acQuire-KL/VT_PCB_PCA/_From_Cornel/Scavenger - V4.4 Cornel 24-09-19/UC_Version4/MFG_PACK -- 3904-30028-06 -- UC_v4.4/BOM_3904-30028-06 - PCA, Scavenger - MCU, ver 4.4.xlsx

Seq | Level | VTPN | Description | ECO | Qty | UoM | RefDes | Populate | BOM Notes | Type | LifeCycle | MFG | MPN | Per Assy. | Unit € | Value € | Vendor | Parts Master Notes | MOQ | Pack Qty | LT
1 | Parent | 3904-30028-06 | PCA, Scavenger - Control (MCU), Ver 4.4 |  | 1 | ea |  |  |  | Make | Production | ECAS | 3904-30028-06 | 1 | 0.0000 | 2.78 |  | 0.0000 | 0 | 0 | 0
2 | 1 | 4200-00020-00 | CAP, 3v7 39mAh Hybrid Layer Capacitor, 15x20, 3-pin Solder Tags |  | 1 | ea | BT1 |  |  | Buy | Production | LongSing Technology | HPC-1520 | 1 | 2.7757 | 2.7757 | LongSing Technology Group | 0.0000 | 500 | 500 | 4
3 | 1 | 4000-00000-00 | Test point / Mounting Hole / Fudicials / Non Component on PCB |  | 1 | ea | BT2 | DNP |  | Reference Item | Production | none | none | 1 | 0.0000 |  |  | 0.0000 | 0 | 0 | 0
4 | 1 | 4106-00020-00 | CAP 0603 (1608_m), 100n, 5%, 25V X7R |  | 8 | ea | C1,C8,C13,C14,C27,C28,C29,C49 |  |  | Buy | Production | Yageo | CC0603JRX7R8BB104 | 8 | 0.0043 | 0.0347 | ECAS | 0.0000 | 4000 | 0 | 16
5 | 1 | 4106-00010-00 | CAP 0603 (1608_m), 10p, 10%, 25V X7R |  | 4 | ea | C2,C3,C50,C51 |  |  | Buy | Production | Kyocera AVX | 06033C100KAT2A | 4 | 0.0019 | 0.0076 | ECAS | 0.0000 | 4000 | 0 | 12
6 | 1 | 4112-00100-00 | CAP 1206 (3216_m), 10u, 10%, 25V X7R |  | 4 | ea | C4,C7,C11,C30 |  |  | Buy | Production | Samsung | CL31B106KAHNFNE | 4 | 0.0254 | 0.1015 | ECAS | 0.0000 | 2000 | 0 | 22
7 | 1 | 4106-00100-00 | CAP 0603 (1608_m), 1u, 10%, 25V X7R |  | 4 | ea | C5,C6,C9,C10 |  |  | Buy | Production | Samsung | CL10B105KA8VPNC | 4 | 0.0140 | 0.0560 | ECAS | 0.0000 | 4000 | 0 | 22
8 | 1 | 4112-00120-00 | CAP 1206 (3216_m), 4u7, 10%, 25V X7R |  | 1 | ea | C12 |  |  | Buy | Production | Taiyo Yuden | MSAST31LAB7475KTNA01 | 1 | 0.0442 | 0.0442 | ECAS | 0.0000 | 2000 | 0 | 19
9 | 1 | 4510-00020-00 | DIO, GP Diode 75V 150mA, SOD-123F |  | 1 | ea | D1 |  |  | Buy | Production | Diotec | 1N4148W | 1 | 0.0121 | 0.0121 | ECAS | 0.0000 | 3000 | 0 | 20
10 | 1 | 4510-00030-00 | DIO, Clamp Ipp TVS, SOD-923 |  | 1 | ea | D2 |  |  | Buy | Production | OnSemi | ESD9B5.0ST5G | 1 | 0.0237 | 0.0237 | 0.0000 | 0.0000 | 8000 | 8000 | 12
11 | 1 | 4000-00000-00 | Test point / Mounting Hole / Fudicials / Non Component on PCB |  | 4 | ea | FID1,FID2,FID3,FID4 | DNP |  | Reference Item | Production | none | none | 4 | 0.0000 |  |  | 0.0000 | 0 | 0 | 0
12 | 1 | 4722-00010-00 | FIL, RLC EMI Filter 3rd Order Low Pass 6 Channel R = 40Ohms, C = 12pF, L = 20nH 16-UFDFN Exposed Pad |  | 1 | ea | FL1 |  |  | Buy | Obsolete | On Semi | CM1624-08DE | 1 | 0.2950 | 0.2950 | ECAS | 0.0000 | 3000 | 0 | 12
13 | 1 | 4000-00000-00 | Test point / Mounting Hole / Fudicials / Non Component on PCB |  | 3 | ea | H1,H2,H3 | DNP |  | Reference Item | Production | none | none | 3 | 0.0000 |  |  | 0.0000 | 0 | 0 | 0
14 | 1 | 4000-00000-00 | Test point / Mounting Hole / Fudicials / Non Component on PCB |  | 1 | ea | J1 | DNP |  | Reference Item | Production | none | none | 1 | 0.0000 |  |  | 0.0000 | 0 | 0 | 0
15 | 1 | 4412-00020-00 | CON, 2x3-pin Turned Contacts, F, THP W2B, P=2.54mm, 3A |  | 1 | ea | J3 |  |  | Buy | Production | Connfly | DS1002-03-2*3131 | 1 | 0.2100 | 0.2100 | ECAS | 0.0000 | 800 | 0 | 30
16 | 1 | 4401-00020-00 | CON, 1x4-pin, Straight, THP, B2B Male Header, P=2.54mm, 3A |  | 1 | ea | J4 |  |  | Buy | Production | Connfly | DS1021-1*4SF11-B | 1 | 0.0198 | 0.0198 | TME | 0.0000 | 2000 | 2000 | 22
17 | 1 | 4750-00010-00 | REL, DPDT-NO (2 Form C) SMD, 3V 46.66mA, 2A |  | 1 | ea | K1 |  |  | Buy | Production | Fujitsu | FTR-B4GA003Z | 1 | 0.8000 | 0.8000 | ECAS | 0.0000 | 1000 | 0 | 14
18 | 1 | 4500-00020-00 | TRN, BJT NPN - Pre-Biased 50 V 100mA 200mW, SMD, SOT-346 |  | 1 | ea | Q2 |  |  | Buy | Production | Rohm | DTC143TKAT146 | 1 | 0.0182 | 0.0182 | ECAS | Confirm Package | 3000 | 0 | 13
19 | 1 | 4006-00170-00 | RES 0603 (1608_m), 10K, 1%, 1/10W, Thick Film |  | 3 | ea | R1,R2,R4 |  |  | Buy | Production | Walsin | WR06X1002FTL | 3 | 0.0012 | 0.0036 | ECAS | 0.0000 | 5000 | 0 | 26
20 | 1 | 4006-00001-00 | RES 0603 (1608_m), 0R (Jumper), 1%, 1/10W, Thick Film |  | 1 | ea | R3 |  |  | Buy | Production | Vishay Dale | CRCW06030000Z0EA | 1 | 0.0010 | 0.0010 | ECAS | 0.0000 | 5000 | 0 | 37
21 | 1 | 4006-00100-00 | RES 0603 (1608_m), 1K, 1%, 1/10W, Thick Film |  | 1 | ea | R64 |  |  | Buy | Production | Walsin | WR06X1001FTL | 1 | 0.0012 | 0.0012 | ECAS | 0.0000 | 5000 | 0 | 26
22 | 1 | 4414-00010-00 | CON, 8-Pos microSD Cage, Hinged, SMD |  | 1 | ea | SD-Card1 |  |  | Buy | Production | Wurth | 693072010801 | 1 | 0.9500 | 0.9500 | Wurth | 0.0000 | 1000 | 1 | 15
23 | 1 | 4751-00010-00 | SWI, Molded Body Reed SPST-NO 10 ~ 30AT Operate Range 10W 500mA (AC/DC) 140V SMD |  | 1 | ea | SW1 |  |  | Buy | Production | Coto Technology | CT10-1030-G1 | 1 | 0.5832 | 0.5832 | Digikey | [04/11/23] Direct ECAS to Digikey pricing | 2000 | 0 | 32
24 | 1 | 4000-00000-00 | Test point / Mounting Hole / Fudicials / Non Component on PCB |  | 1 | ea | TP1 |  |  | Reference Item | Production | none | none | 1 | 0.0000 |  |  | 0.0000 | 0 | 0 | 0
25 | 1 | 4704-00010-00 | MCU, ARM® Cortex®-M33 STM32U5 32-Bit 160MHz 2MB (2M x 8) FLASH 64-LQFP (10x10) |  | 1 | ea | U1 |  |  | Free Issue | Production | ST Micro | STM32U575RIT6 | 1 | 5.7100 | 5.7100 |  | VT purchased 10kpcs @ €5.71 | 1 | 0 | 10
26 | 1 | 4522-00020-00 | REG, 3v3 300mA LDO Linear Voltage Regulator, SOT-25 |  | 2 | ea | U2,U6 |  |  | Buy | Production | Diodes Inc | AP7343DQ-33W5-7 | 2 | 0.0949 | 0.1898 | ECAS | 0.0000 | 3000 | 0 | 8
27 | 1 | 4410-00010-00 | CON, 2x18-Pos, F, PCI, SMD, P=1.00mm, Black |  | 1 | ea | U3 |  |  | Buy | Production | Amphenol | 10061913-100CLF | 1 | 2.2400 | 2.2400 | ECAS | [13/09/23] RFQ to Avnet | 2450 | 1 | 10
28 | 1 | 4718-00010-00 | MEM, EEPROM Memory IC 512Kbit (64x8) I²C 1MHz 900ns 8-SOIC |  | 1 | ea | U4 |  |  | Buy | Production | On Semi | CAT24C512XE-T2 | 1 | 0.7202 | 0.7202 | Digikey | [14/11/23] EBV offer "XI" (-40~+85C not "XE" -40~+125C) 6k EAU, 1k8 reel @ €0.90; 8-weeks. [02/02/24] Alternative packages 8-TSSOP (CAT24C512YI-GT3) @ €0.4865 @ 3k reel | 381 | 0 | 1
29 | 1 | 4720-00010-00 | ICS, Supervisor 3v0VDF N-ch Open Drain 1-Ch SSOT-24 |  | 1 | ea | U9 |  |  | Buy | Production | Torex | XC6120N302NR-G | 1 | 0.1800 | 0.1800 | ECAS | 0.0000 | 1000 | 1000 | 18
30 | 1 | 4714-00020-00 | CRY, 16MHz ±10ppm Crystal 10pF 80Ohms 4-SMD, No Lead |  | 1 | ea | XTAL1 |  |  | Buy | Production | CTS Frequency Controls | 403C11A16M00000 | 1 | 0.3187 | 0.3187 | ECAS | [07/12/23] Jauch offer O 16,0-JXS32-10-10/10-LF 1k @ $0.35 | 3000 | 0 | 12
31 | 1 | 4714-00010-00 | CRY, 32.768kHz ±10ppm 6pF 70kOhms 2-SMD, No Lead |  | 1 | ea | Y1 |  |  | Buy | Production | ECS Inc | ECS-.327-6-34B-C-TR | 1 | 0.3777 | 0.3777 | Digikey | [07/12/23] Jauch offer Q 0,032768-JTX310-6-10-T1-LF 1k @ $0.25 | 3000 | 0 | 15
32 | 1 | 4904-30028-05 | PCB, Scavenger MCU (32x107x1.6mm, 4L, 1ox/1oz, ENIG, 4-up), ver4.4 |  | 1 | ea | PCB1 |  |  | Buy | Production | EMS Approved | 4904-30028-05 | 1 | 1.0000 | 1.0000 | 0.0000 | 0.0000 | 0 | 0 | 0
