acQuire-KL/VT_PCB_PCA/_From_Cornel/Scavenger - V4.4 Cornel 24-10-31/BG95_Version4_4L/MFG_PACK 3902-30029-07/3902-30029-07_BOM -- Comms BG95 v4.4.xlsx

Sheet: BOM
Seq | Level | VTPN | Description | ECO | Qty | UoM | RefDes | Populate | BOM Notes | Type | LifeCycle | MFG | MPN | Per Assy. | Unit € | Value € | Vendor | Parts Master Notes | MOQ | Pack Qty | LT
1 | Parent | 3902-30029-07 | PCA, Scavenger - Communications (GSM), BG95, Ver 4.4 - EUR |  | 1 | ea |  |  |  | Make | Production | ECAS | 0.00 | 1 | 0.0000 | 16.03 |  | 0.0000 | 0 | 0 | 0
2 | 1 | 4200-00020-00 | CAP, 3v7 39mAh Hybrid Layer Capacitor, 15x20, 3-pin Solder Tags |  | 1 | ea | BT1 |  |  | Buy | Production | LongSing Technology | HPC-1520 | 1 | 2.6969 | 2.6969 | LongSing Technology Group | 0.0000 | 500 | 500 | 0
3 | 1 | 4106-00040-00 | CAP 0603 (1608_m), 33p, 5%, 50V NP0 |  | 3 | ea | C1,C2,C3 |  |  | Buy | Production | Darfon | C1608NP0330JGTS | 3 | 0.0019 | 0.0058 | ECAS | 0.0000 | 4000 | 4000 | 0
4 | 1 | 4106-00020-00 | CAP 0603 (1608_m), 100n, 10%, 16V X7R |  | 3 | ea | C4,C7,C8 |  |  | Buy | Production | Darfon | C1005X7R104KETS | 3 | 0.0005 | 0.0015 | Schukat | 0.0000 | 4000 | 4000 | 0
5 | 1 | 4128-00100-00 | CAP 2917 (7343_m), 470u, 10%, 6v3 Tant |  | 2 | ea | C5,C6 |  |  | Buy | Production | Kyocera AVX | TAJD477K006RNJ | 2 | 0.5600 | 1.1200 | ECAS | 0.0000 | 500 | 500 | 0
6 | 1 | 4106-00040-00 | CAP 0603 (1608_m), 33p, 5%, 50V NP0 |  | 2 | ea | C9,C10 | DNP |  | Buy | Production | Darfon | C1608NP0330JGTS | 2 | 0.0019 | 0.0039 | ECAS | 0.0000 | 4000 | 4000 | 0
7 | 1 | 4106-00010-00 | CAP 0603 (1608_m), 10p, 5%, 50V NP0 |  | 2 | ea | C11,C12 |  |  | Buy | Production | Darfon | C1608NP0100JGTS | 2 | 0.0019 | 0.0038 | ECAS | 0.0000 | 4000 | 4000 | 0
8 | 1 | 4006-00000-00 | RES 0603 Place Holder |  | 2 | ea | C13,C14 | DNP |  | Reference Item | Production | none | none | 2 | 0.0000 |  |  | 0.0000 | 0 | 0 | 0
9 | 1 | 4724-00010-00 | TVS, 5-Ch, 12.5V Clamp 8A (8/20µs) Ipp, SC-70-6 |  | 1 | ea | D1 |  |  | Buy | Production | Semtech | SMF05C.TCT | 1 | 0.2448 | 0.2448 | ECAS | 0.0000 | 3000 | 0 | 0
10 | 1 | 4000-00000-00 | Test point / Mounting Hole / Fudicials / Non Component on PCB |  | 4 | ea | FID1,FID2,FID3,FID4 |  |  | Reference Item | Production | none | none | 4 | 0.0000 |  |  | 0.0000 | 0 | 0 | 0
11 | 1 | 4000-00000-00 | Test point / Mounting Hole / Fudicials / Non Component on PCB |  | 1 | ea | H1 |  |  | Reference Item | Production | none | none | 1 | 0.0000 |  |  | 0.0000 | 0 | 0 | 0
12 | 1 | 4402-00020-00 | CON, 2x5-pin, Straight, SMD, B2B Male Header, P=2.54mm, 3A |  | 1 | ea | J2 |  |  | Buy | Production | Amphenol FCI | 95278-102B10LF | 1 | 0.3668 | 0.3668 | ECAS | 0.0000 | 5000 | 0 | 0
13 | 1 | 4402-00030-00 | CON, 2x8-pin, Straight, SMD, B2B Male Header, P=2.54mm, 3A |  | 1 | ea | J3 |  |  | Buy | Production | Amphenol FCI | 95278-102B16LF | 1 | 0.4309 | 0.4309 | ECAS | 0.0000 | 1 | 0 | 0
14 | 1 | 4753-00010-00 | HDW, Cable Clamp, SMD, 5x5x2mm, Ø1.0 ~ 1.5mm |  | 3 | ea | J4,J5,J6 |  |  | Buy | Production | Harwin | S8111-46R | 3 | 0.1331 | 0.3994 | Digikey | 0.0000 | 1500 | 1500 | 0
15 | 1 | 4414-00020-00 | CON, 6-Pos MicroSIM Cage, Push-Pull, No Detect, SMD |  | 1 | ea | J11 |  | • Fit "Test SIM" before starting initial Test • Replace with "Final SIM" after passing Test | Buy | Production | Molex | 78646-3001 | 1 | 0.7900 | 0.7900 | ECAS | RFQ before next build | 57 | 1 | 0
16 | 1 | 4416-00010-00 | CON, U.FL (UMCC) Jack, Male Pin 50Ohm SMD |  | 1 | ea | J12 |  |  | Buy | Production | TE Connectivity | 2337019-1 | 1 | 0.0061 | 0.0061 | ECAS | 0.0000 | 55 | 1 | 0
17 | 1 | 4500-00020-00 | TRN, BJT NPN - Pre-Biased R1=4K7 R2=0R, Vce=50V 100mA 200mW, SMD, TO-236-3, SC-59, SOT-23-3 |  | 3 | ea | Q1,Q3,Q8 |  |  | Buy | Production | Rohm | DTC143TKAT146 | 3 | 0.0182 | 0.0547 | ECAS | Confirm Package | 3000 | 0 | 0
18 | 1 | 4530-00010-00 | FET, P-Channel 30 V 6.5A (Ta) 3.1W (Ta), 8-SOP |  | 1 | ea | Q2 |  |  | Buy | Production | UMW | AO4459 | 1 | 0.0630 | 0.0630 | ECAS | 0.0000 | 500 | 1 | 0
19 | 1 | 4006-00160-00 | RES 0603 (1608_m), 15K, 1%, 1/10W, Thick Film |  | 1 | ea | R1 |  |  | Buy | Production | Vishay | CRCW060315K0FKEA | 1 | 0.0010 | 0.0010 | Schukat | 0.0000 | 5000 | 5000 | 0
20 | 1 | 4006-00150-00 | RES 0603 (1608_m), 4K7, 1%, 1/10W, Thick Film |  | 2 | ea | R2,R3 |  |  | Buy | Production | Vishay | CRCW06034K70FKEA | 2 | 0.0012 | 0.0023 | Schukat | 0.0000 | 5000 | 5000 | 0
21 | 1 | 4006-00001-00 | RES 0603 (1608_m), 0R (Jumper), 1%, 1/10W, Thick Film |  | 1 | ea | R4 |  |  | Buy | Production | Vishay Dale | CRCW06030000Z0EA | 1 | 0.0009 | 0.0009 | Schukat | 0.0000 | 5000 | 5000 | 0
22 | 1 | 4000-00000-00 | Test point / Mounting Hole / Fudicials / Non Component on PCB |  | 1 | ea | TP1 |  |  | Reference Item | Production | none | none | 1 | 0.0000 |  |  | 0.0000 | 0 | 0 | 0
23 | 1 | 4716-00010-00 | MDM, Cellular, GSM, LTE Transceiver Module 850MHz, 900MHz, 1.8GHz, 1.9GHz, SMD Module, No Antenna |  | 1 | ea | U1 |  |  | Buy | Production | Quectel | BG95M3LA-64-SGNS | 1 | 8.6749 | 8.6749 | FMG Electronics | [21/11/23] FMG revised quote from 1k @ $11.29 to 4k @ $9.80 with 1k schedule; allow 250pcs shipments. [22/11/23] FMG revised 4k $9.80 to $9.65 [28/11/23] FMG offer 1k @ $9.80 [12/12/23] FMG to keep 1k EAU @ $9.65 (4x 250pcs drops) | 1000 | 250 | 0
24 | 1 | 4702-00010-00 | IC, 4-Bit Bi-Directional Tri-State Level Shifter, Auto Detect Direction, 12-UQFN |  | 1 | ea | U2 |  |  | Buy | Production | TI | TXB0104RUT | 1 | 0.2430 | 0.2430 | ECAS | [14/12/23] EBV offerNXB0104GU12X 8k EAU, 4k reel @ €0.23; 8-weeks | 100 | 1 | 0
25 | 1 | 4902-30029-06 | PCB, Scavenger GSM, BG95 (71.00x25.50mm, 4-L, Cu, ENIG), ver 4.4 |  | 1 | ea | PCB1 |  |  | Buy | Production | EMS Approved | 0.00 | 1 | 0.9200 | 0.9200 | 0.0000 | 0.0000 | 0 | 0 | 0

Sheet: ECO History
RefDes | VTPN | Parent Rev | Action | ECO | Date | Description | Comment
 |  | 04 | Initial Release |  | 2024-04-18 | #N/A
 |  | 05 |  |  |  | #N/A
 |  | 06 |  |  | 2024-04-18 | #N/A
 |  | 07 |  |  | 2024-10-31 | #N/A
 |  |  |  |  |  | #N/A
 |  |  |  |  |  | #N/A
