acQuire-KL/VT_PCB_PCA/_From_Cornel/Scavenger - V4.4 Cornel 24-09-19/Main_V44 -Temp/MFG_PACK -- 3905-30027-06/3905-30027-06_BOM -- Main_V4.4.xlsx

Sheet: BOM
Seq | Level | VTPN | Description | ECO | Qty | UoM | RefDes | Populate | BOM Notes | Type | LifeCycle | MFG | MPN | Per Assy. | Unit € | Value € | Vendor | Parts Master Notes | MOQ | Pack Qty | LT
1 | Parent | 3905-30027-06 | PCA, Scavenger - Main (MAIN), No Temp, Ver 4.4.1 |  | 1 | ea |  |  |  | Make | Production | ECAS | 0.00 | 1 | 0.0000 | #N/A |  | 0.0000 | 0 | 0 | 0
2 | 1 | 4106-00020-00 | CAP 0603 (1608_m), 100n, 10%, 16V X7R |  | 25 | ea | C1,C3,C5,C10,C12,C15,C20,C21,C24,C25,C27,C28,C29,C33,C34,C35,C36,C37,C38,C39,C40,C55,C56,C57,C58 |  |  | Buy | Production | Darfon | C1005X7R104KETS | 25 | 0.0005 | 0.0123 | Schukat | 0.0000 | 4000 | 4000 | 0
3 | 1 | 4112-00110-00 | CAP 1206 (3216_m), 10u, 10%, 16v, X7R |  | 3 | ea | C2,C11,C53 |  |  | Buy | Production | Samsung | CL31B106KOHNFNE | 3 | 0.0256 | 0.0768 | ECAS | 0.0000 | 2000 | 0 | 0
4 | 1 | 4106-00030-00 | CAP 0603 (1608_m), 1n, 10%, 50V X7R |  | 3 | ea | C4,C6,C7 |  |  | Buy | Production | Darfon | C1608X7R102KGTS | 3 | 0.0020 | 0.0060 | Schukat | 0.0000 | 4000 | 4000 | 0
5 | 1 | 4112-00150-00 | CAP 1206 (3216_m), 22u, 10%, 6v3 X7R |  | 4 | ea | C8,C9,C13,C14 |  |  | Buy | Production | Walsin | 1206B226K6R3CT | 4 | 0.0720 | 0.2880 | ECAS | 0.0000 | 2000 | 0 | 0
6 | 1 | 4112-00100-00 | CAP 1206 (3216_m), 10u, 10%, 25V X7R |  | 3 | ea | C17,C18,C19 |  |  | Buy | Production | Samsung | CL31B106KAHNFNE | 3 | 0.0254 | 0.0761 | ECAS | 0.0000 | 2000 | 0 | 0
7 | 1 | 4106-00100-00 | CAP 0603 (1608_m), 1u, 10%, 25V X7R |  | 6 | ea | C22,C23,C26,C30,C31,C32 |  |  | Buy | Production | Samsung | CL10B105KA8VPNC | 6 | 0.0024 | 0.0144 | ECAS | 0.0000 | 1000 | 1 | 0
8 | 1 | 4106-00010-00 | CAP 0603 (1608_m), 10p, 5%, 50V NP0 |  | 2 | ea | C41,C44 |  |  | Buy | Production | Darfon | C1608NP0100JGTS | 2 | 0.0019 | 0.0038 | ECAS | 0.0000 | 4000 | 4000 | 0
9 | 1 | 4106-00100-00 | CAP 0603 (1608_m), 1u, 10%, 25V X7R |  | 1 | ea | C42 |  |  | Buy | Production | Samsung | CL10B105KA8VPNC | 1 | 0.0024 | 0.0024 | ECAS | 0.0000 | 1000 | 1 | 0
10 | 1 | 4106-00020-00 | CAP 0603 (1608_m), 100n, 10%, 16V X7R |  | 5 | ea | C43,C47,C48,C49,C50 |  |  | Buy | Production | Darfon | C1005X7R104KETS | 5 | 0.0005 | 0.0024 | Schukat | 0.0000 | 4000 | 4000 | 0
11 | 1 | 4106-00015-00 | CAP 0603 (1608_m), 10n, 10%, 50V X7R |  | 2 | ea | C45,C46 |  |  | Buy | Production | Darfon | C1608X7R103KGTS | 2 | 0.0021 | 0.0042 | Schukat | 0.0000 | 4000 | 4000 | 0
12 | 1 | 4106-00050-00 | CAP 0603 (1608_m), 4n7, 1%, 25V X8R |  | 1 | ea | C51 |  |  | Buy | Production | Walsin | 0603B472K250CT | 1 | 0.0064 | 0.0064 | Digikey | 0.0000 | 4000 | 4000 | 0
13 | 1 | 4130-00010-00 | CAP, 0.22u Poly (PP) Metalised 310vac 630vdc THP, P=22.50mm, 26.00x7.00mmx16.00mm |  | 1 | ea | C52 |  |  | Buy | Production | Kemet | F862DI224K310ZLH0J | 1 | 0.3770 | 0.3770 | ECAS | 0.0000 | 1 | 0 | 0
14 | 1 | 4510-00010-00 | DIO, Fast Avalanche Diode 1kv 1A5, DO-214AC (SMA) |  | 3 | ea | D4,D5,D6 |  |  | Buy | Production | Vishay | BYG21M-E3/TR | 3 | 0.0650 | 0.1950 | EBV | [14/12/23] EBV 10k8 EAU, 1k8 reel @ €0.065; 9-weeks | 10800 | 1800 | 0
15 | 1 | 4408-00030-00 | CON, 1x4-Pin, M, R/A, SMD, W2B, 4-Shroud, H=6.00mm, P=2.50mm, 3A 250V |  | 1 | ea | J1 |  |  | Buy | Production | Zhejiang Lianhe Electronics Co Ltd | A2501-SR04-XH4AWB | 1 | 0.0494 | 0.0494 | ECO Cables | ECO Cable supply with 3404-00030-00 | 700 | 700 | 0
16 | 1 | 4402-10021-00 | CON, 2x8-pin, Straight, SMD, B2B Female, P=2.54mm, H=7.34mm, 1A |  | 1 | ea | J2 |  |  | Buy | Production | MPE Garry | 098-6-016-0-NFX-YT0 | 1 | 1.2500 | 1.2500 | ECAS | 0.0000 | 58 | 1 | 0
17 | 1 | 4402-10011-00 | CON, 2x5-pin, Straight, SMD, B2B Female, P=2.54mm, H=7.34mm, 1A |  | 1 | ea | J3 |  |  | Buy | Production | MPE Garry | 098-6-010-0-NFX-YT0 | 1 | 0.6300 | 0.6300 | ECAS | 0.0000 | 69 | 1 | 0
18 | 1 | 4401-00050-00 | CON, 1x6-pin, Straight, THT, B2B Female, P=2.54mm, H=8.50mm, 3A |  | 2 | ea | J4,J13 |  |  | Buy | Production | Connfly | ZL262-6SG / DS1023-1*6S21 | 2 | 0.0366 | 0.0732 | TME | 0.0000 | 500 | 10 | 0
19 | 1 | 4400-00015-00 | CON, 2x3-pin, R/A, THP, B2B Header, P=2.54mm, 3A |  | 1 | ea | J5 |  |  | Buy | Production | Wurth | 61300621021.00 | 1 | 0.0720 | 0.0720 | ECAS | 0.0000 | 55 | 1 | 0
20 | 1 | 4000-00000-00 | Test point / Mounting Hole / Fudicials / Non Component on PCB |  | 18 | ea | J6,J8,J9,J10,J11,J12,J14,J16,J17,J18,J19,J20,J22,J23,J24,J25,J26,J32 |  |  | Reference Item | Production | none | none | 18 | 0.0000 |  |  | 0.0000 | 0 | 0 | 0
21 | 1 | 4000-00000-00 | Test point / Mounting Hole / Fudicials / Non Component on PCB |  | 1 | ea | J7 |  |  | Reference Item | Production | none | none | 1 | 0.0000 |  |  | 0.0000 | 0 | 0 | 0
22 | 1 | 4412-00050-00 | CON, 1x9-pin Turned Contacts, F, THP W2B, H=7.50mm, P=2.54mm, 3A |  | 1 | ea | J15 |  |  | Buy | Production | Connfly | DS1002-03-1*9131 | 1 | 0.0478 | 0.0478 | TME | 0.0000 | 1000 | 10 | 0
23 | 1 | 4401-00040-00 | CON, 1x3-pin, Straight, THT, B2B Female, P=2.54mm, H=8.50mm, 3A |  | 1 | ea | J21 |  |  | Buy | Production | Connfly | ZL262-3SG / DS1023-1*3S21 | 1 | 0.0385 | 0.0385 | TME | 0.0000 | 520 | 10 | 0
24 | 1 | 4420-20010-00 | CON, Terminal Block, 2-Pos THT, 30AWG, P=5.08mm, H=10.00mm |  | 2 | ea | J27,J28 |  |  | Buy | Production | TE Connectivity | 282837-2 | 2 | 0.3430 | 0.6860 | 0.0000 | 0.0000 | 1200 | 1200 | 0
25 | 1 | 4753-00010-00 | HDW, Cable Clamp, SMD, 5x5x2mm, Ø1.0 ~ 1.5mm |  | 1 | ea | J29 |  |  | Buy | Production | Harwin | S8111-46R | 1 | 0.1331 | 0.1331 | Digikey | 0.0000 | 1500 | 1500 | 0
26 | 1 | 4753-00010-00 | HDW, Cable Clamp, SMD, 5x5x2mm, Ø1.0 ~ 1.5mm |  | 2 | ea | J30,J31 |  |  | Buy | Production | Harwin | S8111-46R | 2 | 0.1331 | 0.2663 | Digikey | 0.0000 | 1500 | 1500 | 0
27 | 1 | 4750-00010-00 | REL, DPDT-NO (2 Form C) SMD, 3V 46.66mA, 2A |  | 1 | ea | K1 |  |  | Buy | Production | Fujitsu | FTR-B4GA003Z | 1 | 0.8000 | 0.8000 | ECAS | 0.0000 | 500 | 1 | 0
28 | 1 | 4300-00010-00 | IND, 330nH Shielded Molded 1.9 A 84mOhm Max Nonstandard |  | 2 | ea | L1,L2 |  |  | Buy | Production | Wurth | 744383130033 | 2 | 0.3720 | 0.7440 | ECAS | 0.0000 | 1000 | 1 | 0
29 | 1 | 4300-00020-00 | IND, 22 µH Unshielded Drum Core, Wirewound 780 mA 351mOhm Max 1210 (3225 Metric) |  | 1 | ea | L3 |  |  | Buy | Production | Taiyo Yuden | CBC3225T220MR | 1 | 0.1037 | 0.1037 | 0.0000 | 0.0000 | 1000 | 1000 | 0
30 | 1 | 4752-00010-00 | LED, Green Diffused, 2v9 20mA, 12550mcd, 525nm, 4-PLCC 3.20 x 2.80 x 3.65mm Domed |  | 3 | ea | LED1,LED2,LED3 |  |  | Buy | Production | CreeLED Inc | CLM2D-GPC-CB0E0793 | 3 | 0.1488 | 0.4464 | ECAS | 0.0000 | 2300 | 0 | 0
31 | 1 | 4520-30010-00 | REG, AC-DC 1 o/p 5v 3A, 85~528VAC i/p THP |  | 1 | ea | PS1 |  |  | Free Issue | Production | Recom Power | RAC15-05SK/480 | 1 | 11.5000 | 11.5000 |  | [08/10/23] VT purchased 3,000 @ €11.50 | 3000 | 11 | 0
32 | 1 | 4520-20010-00 | REG, DC-DC Isolated 1 o/p 5v 4v5, 9v i/p, THP |  | 1 | ea | PS2 |  |  | Free Issue | Production | Traco Power | THM 10-0511 | 1 | 19.9389 | 19.9389 |  | [01/08/23] VT Purchased 110pcs @ €32.16 [01/09/23] Astute offered P-Duke; 1k @ £22.75 (€26.13) EXW UK [4520-20030-00] [09/10/23] Arrow revised to $22.18 (~€20.52) on 10K EAU [11/12/23] Arrow offer $25.85 (~€23.91) on 1k EAU | 1000 | 1000 | 0
33 | 1 | 4520-20022-00 | REG, DC-DC Isolated 1 o/p 5V 400mA 4.5V - 5.5V Input, SMD |  | 1 | ea | PS3 |  |  | Buy | Production | Murata | NXE2S0505MC-R7 | 1 | #N/A | #N/A | 0.0000 | 0.0000 | 0 | 0 | 0
34 | 1 | 4500-00020-00 | TRN, BJT NPN - Pre-Biased R1=4K7 R2=0R, Vce=50V 100mA 200mW, SMD, TO-236-3, SC-59, SOT-23-3 |  | 1 | ea | Q1 |  |  | Buy | Production | Rohm | DTC143TKAT146 | 1 | 0.0182 | 0.0182 | ECAS | Confirm Package | 3000 | 0 | 0
35 | 1 | 4500-00030-00 | TRN, BJT NPN - Pre-Biased R1=4K7 R2=4K7, Vce=50V 100mA 200mW, SMD, TO-236-3, SC-59, SOT-23-3 |  | 3 | ea | Q2,Q3,Q4 |  |  | Buy | Production | Rohm | DTC143EKAT146 | 3 | #N/A | #N/A | 0.0000 | 0.0000 | 0 | 0 | 0
36 | 1 | 4006-00030-00 | RES 0603 (1608_m), 10R, 1%, 1/10W, Thick Film |  | 3 | ea | R1,R4,R16 |  |  | Buy | Production | Vishay | CRCW060310R0FKEA | 3 | 0.0014 | 0.0041 | Schukat | 0.0000 | 5000 | 5000 | 0
37 | 1 | 4006-00300-00 | RES 0603 (1608_m), 3K, 1%, 1/10W, Thick Film |  | 21 | ea | R2,R3,R15,R22,R27,R28,R29,R30,R31,R32,R36,R37,R38,R39,R40,R41,R42,R43,R48,R49,R50 |  |  | Buy | Production | Stackpole | RMCF0603FT3K00 | 21 | 0.0004 | 0.0088 | ECAS | 0.0000 | 5000 | 5000 | 0
38 | 1 | 4018-01000-00 | RES 2512 (6332_m), 249K, 0.1%, 0.5W, Thick Film |  | 12 | ea | R5,R6,R7,R8,R10,R11,R12,R13,R17,R18,R19,R20 |  |  | Buy | Production | Viking | AR12BTCU2493 | 12 | 0.0990 | 1.1880 | ECAS | 0.0000 | 900 | 10 | 0
39 | 1 | 4006-00040-00 | RES 0603 (1608_m), 150R, 1%, 1/10W, Thick Film |  | 3 | ea | R9,R14,R21 |  |  | Buy | Production | Vishay | CRCW0603150RFKEA | 3 | 0.0005 | 0.0016 | Schukat | 0.0000 | 5000 | 5000 | 0
40 | 1 | 4006-00150-00 | RES 0603 (1608_m), 4K7, 1%, 1/10W, Thick Film |  | 2 | ea | R23,R24 |  |  | Buy | Production | Vishay | CRCW06034K70FKEA | 2 | 0.0012 | 0.0023 | Schukat | 0.0000 | 5000 | 5000 | 0
41 | 1 | 4006-00130-00 | RES 0603 (1608_m), 1K3, 1%, 1/10W, Thick Film |  | 1 | ea | R25 |  |  | Buy | Production | Stackpole | RMCF0603FT1K30 | 1 | 0.0005 | 0.0005 | ECAS | 0.0000 | 5000 | 5000 | 0
42 | 1 | 4006-00140-00 | RES 0603 (1608_m), 1K5, 1%, 1/10W, Thick Film |  | 1 | ea | R26 |  |  | Buy | Production | Vishay | CRCW06031K50FKEA | 1 | 0.0004 | 0.0004 | Schukat | 0.0000 | 5000 | 5000 | 0
43 | 1 | 4006-00470-00 | RES 0603 (1608_m), 47K, 1%, 1/10W, Thick Film |  | 1 | ea | R33 |  |  | Buy | Production | Vishay | CRCW060347K0FKEA | 1 | 0.0005 | 0.0005 | Schukat | 0.0000 | 5000 | 5000 | 0
44 | 1 | 4006-00200-00 | RES 0603 (1608_m), 2K, 0.1%, 1/10W, Thick Film |  | 4 | ea | R34,R51,R52,R53 |  |  | Buy | Production | Yageo | RT0603BRD072KL | 4 | 0.0120 | 0.0480 | ECAS | 0.0000 | 5000 | 5000 | 0
45 | 1 | 4006-00100-00 | RES 0603 (1608_m), 1K, 1%, 1/10W, Thick Film |  | 1 | ea | R35 |  |  | Buy | Production | Vishay | CRCW06031K00FKEA | 1 | 0.0004 | 0.0004 | Schukat | 0.0000 | 5000 | 5000 | 0
46 | 1 | 4006-00160-00 | RES 0603 (1608_m), 15K, 1%, 1/10W, Thick Film |  | 3 | ea | R44,R45,R46 |  |  | Buy | Production | Vishay | CRCW060315K0FKEA | 3 | 0.0010 | 0.0030 | Schukat | 0.0000 | 5000 | 5000 | 0
47 | 1 | 4006-00010-00 | RES 0603 (1608_m), 47R, 1%, 1/10W, Thick Film |  | 1 | ea | R47 |  |  | Buy | Production | Vishay | CRCW060347R0FKEA | 1 | 0.0005 | 0.0005 | Schukat | 0.0000 | 5000 | 5000 | 0
48 | 1 | 4006-00020-00 | RES 0603 (1608_m), 220R, 1%, 1/10W, Thick Film |  | 3 | ea | R71,R72,R73 |  |  | Buy | Production | Vishay | CRCW0603220RFKEA | 3 | 0.0010 | 0.0030 | ECAS | 0.0000 | 5000 | 0 | 0
49 | 1 | 4022-00010-00 | VAR, 820 V 1.2 kA Varistor 1 Circuit, 4032 (10182_m), No Lead |  | 3 | ea | RV1,RV2,RV3 |  |  | Buy | Production | Eaton | MOVS4032V510 | 3 | 0.3350 | 1.0050 | ECAS | 0.0000 | 900 | 0 | 0
50 | 1 | 4000-00000-00 | Test point / Mounting Hole / Fudicials / Non Component on PCB |  | 1 | ea | TP1 |  |  | Reference Item | Production | none | none | 1 | 0.0000 |  |  | 0.0000 | 0 | 0 | 0
51 | 1 | 4520-10010-00 | REG, Buck Switching Positive Adjustable 0.8V 1 Output 2.5A SOT-563, SOT-666 |  | 2 | ea | U1,U8 |  |  | Buy | Production | Diodes Inc | AP62250Z6-7 | 2 | 0.2400 | 0.4800 | ECAS | RFQ before next build | 250 | 1 | 0
52 | 1 | 4700-00010-00 | IC, 2/2 Transceiver, Isolated Half RS422, RS485 16-SOIC |  | 1 | ea | U2 |  |  | Buy | Production | TI | ISO3082DWR | 1 | 2.2474 | 2.2474 | ECAS | 0.0000 | 100 | 1 | 0
53 | 1 | 4708-00021-00 | OPA, General Purpose Op Amp 2-Circuit 8-SOIC |  | 3 | ea | U3,U12,U13 |  |  | Buy | Production | TI | LM358BAIDR | 3 | 0.0414 | 0.1241 | TI.com | 0.0000 | 2500 | 2500 | 0
54 | 1 | 4710-00010-00 | AMP, 250mV Isolated Amp, isolated output |  | 3 | ea | U4,U6,U7 |  |  | Free Issue | Production | TI | AMC1400DWLR | 3 | 4.1000 | 12.3000 |  | 0.0000 | 500 | 1 | 0
55 | 1 | 4522-00010-00 | REG, 5v 100mA 1x Fixed Linear o/p, SOT-89-3 |  | 1 | ea | U5 |  |  | Buy | Production | ST Micro | L78L05ACUTR | 1 | 0.1980 | 0.1980 | ECAS | 0.0000 | 2500 | 0 | 0
56 | 1 | 4700-00030-00 | IC, Single 2-Line to 1-Line Data Selector/Multiplexer, VSSOP-8 |  | 1 | ea | U9 |  |  | Buy | Production | TI | SN74LVC2G157DCU | 1 | 0.3326 | 0.3326 | ECAS | 0.0000 | 100 | 1 | 0
57 | 1 | 4706-00040-00 | IC, RTD to Digital converter, TQFN-20 |  | 2 | ea | U11,U20 |  |  | Buy | Production | Analog Devices | MAX31865ATP+T | 2 | 3.5329 | 7.0658 | ADI.com | 0.0000 | 500 | 1 | 0
58 |  | 4410-00010-00 | CON, 2x18-Pos, F, PCI, SMD, P=1.00mm, Black |  | 6 | ea | U14,U15,U16,U17,U18,U19 |  |  | Buy | Production | Amphenol | 10061913-100PLF | 6 | 1.3100 | 7.8600 | ECAS | 0.0000 | 400 | 1 | 0
59 |  | 4520-00020-01 | ICS, 100mA switched capacitor charge-pump voltage converter 1.5v~5.5v Input, -Vin Output, 8-SOIC |  | 1 | ea | U21 |  |  | Buy | Production | TI | LM2660MX/NOPB | 1 | 0.4704 | 0.4704 | ECAS | 0.0000 | 2500 | 2500 | 0
60 |  | 4704-00020-00 | MCU, Capacitive-touch, 16 I/O (16 sensors), 8-KB FRAM, 2-KB SRAM, 27 I/O and 12-bit ADC, VQFN32 |  | 1 | ea | U22 |  |  | Buy | Production | TI | MSP430FR2672TRHBR | 1 | 1.4239 | 1.4239 | TI.com | 0.0000 | 1000 | 250 | 0
61 |  | 4714-00010-00 | CRY, 32.768kHz ±10ppm 6pF 70kOhms 2-SMD, No Lead |  | 1 | ea | Y1 |  |  | Buy | Production | ECS Inc | ECS-.327-6-34B-C-TR | 1 | 0.3777 | 0.3777 | Digikey | [07/12/23] Jauch offer Q 0,032768-JTX310-6-10-T1-LF 1k @ $0.25 | 3000 | 0 | 0
62 |  | 4905-30027-06 | PCB, Scavenger MAIN (90x190x1.6mm, 4L, 1oz/1oz, ENIG, 2-up), ver4.4 |  | 1 | ea |  |  |  | Buy | Production | EMS Approved | 0.00 | 1 | 4.9200 | 4.9200 | 0.0000 | 0.0000 | 1000 | 1000 | 0

Sheet: ECO History
RefDes | VTPN | Parent Rev | Action | ECO | Date | Description | Comment
 |  | 00 | Initial Release |  | 2024-10-09 | #N/A
J30 | 4753-00010-00 | 06 | Remove |  | 2024-11-08 | HDW, Cable Clamp, SMD, 5x5x2mm, Ø1.0 ~ 1.5mm | Not required in this Variant
J31 | 4753-00010-00 | 06 | Remove |  | 2024-11-08 | HDW, Cable Clamp, SMD, 5x5x2mm, Ø1.0 ~ 1.5mm | Not required in this Variant
J27 | 4420-20010-00 | 06 | Remove |  | 2024-11-08 | CON, Terminal Block, 2-Pos THT, 30AWG, P=5.08mm, H=10.00mm | Not required in this Variant
J28 | 4420-20010-00 | 06 | Remove |  | 2024-11-08 | CON, Terminal Block, 2-Pos THT, 30AWG, P=5.08mm, H=10.00mm | Not required in this Variant
 |  |  |  |  |  | #N/A
 |  |  |  |  |  | #N/A
