acQuire-KL/VT_PCB_PCA/_From_Cornel/Scavenger - V4.4 Cornel 24-09-19/ADE_Main/MFG_PACK -- 3901-30030-05 -- ADE Main, v4.4/3901-30030-05_BOM -- ADE_Main_V4.4.xlsx

Sheet: Scavenger BOM
Seq | Level | VTPN | Description | ECO | Qty | UoM | RefDes | Populate | BOM Notes | Type | LifeCycle | MFG | MPN | Per Assy. | Unit € | Value € | Vendor | Parts Master Notes | MOQ | Pack Qty | LT
1 | Parent | 3901-30030-05 | PCA, Scavenger - ADE Channel (ADE), ver 4.4 |  | 1 | ea |  |  |  | Make | Production | ECAS | 3901-30030-05 | 1 | 0.0000 | 0.01 |  | 0.0000 | 0 | 0 | 0
2 | 1 | 4104-00020-00 | CAP 0402 (1005_m), 22n, 10%, 25V X7R |  | 5 | ea | C1,C3,C7,C9,C11 |  |  | Buy | Production | Kemet | C0402C223J3RAC7867 | 5 | 0.0019 | 0.0097 | ECAS | 0.0000 | 5000 | 5000 | 0
3 | 1 | 4104-00100-00 | CAP 0402 (1005_m), 0.1u, 10%, 25V X7R | 24-ECO-012 | 15 | ea | C2,C5,C6,C13,C14,C15,C16,C17,C19,C21,C23,C27,C28,C29,C30 |  |  | Buy | Production | Murata | GRM155R71E104KE14D | 15 | 0.0030 | 0.0450 | ECAS | 0.0000 | 5000 | 5000 | 0
4 | 1 | 4004-00000-00 | RES 0402 Place Holder |  | 4 | ea | C4,C8,C10,C12 | DNP |  | Reference Item | Production | none | none | 4 | #N/A |  |  | 0.0000 | 0 | 0 | 0
5 | 1 | 4112-00100-00 | CAP 1206 (3216_m), 10u, 10%, 25V X7R |  | 6 | ea | C18,C20,C22,C24,C25,C26 |  |  | Buy | Production | Samsung | CL31B106KAHNFNE | 6 | 0.0254 | 0.1523 | ECAS | 0.0000 | 2000 | 0 | 0
6 | 1 | 4000-00000-00 | Test point / Mounting Hole / Fudicials / Non Component on PCB |  | 4 | ea | FID1,FID2,FID3,FID4 | DNP |  | Reference Item | Production | none | none | 4 | 0.0000 |  |  | 0.0000 | 0 | 0 | 0
7 | 1 | 4408-00010-00 | CON, 1x8-Pin, M, R/A, SMD, W2B, 4-Shroud, 2.50mm, 3A 250V |  | 1 | ea | J1 |  |  | Buy | Production | Zhejiang Lianhe Electronics Co Ltd | A2501-SR08-XH8AWB | 1 | 0.0000 | 0.0000 | ECO Cables | [12/09/2023] Zhejiang Lianhe offer 1k @ $0.0389, 10k @ €0.0354 [12/12/2023] Supplied with M12 Pre-Wired Assembly by Eco Cables China | 1000 | 1000 | 0
8 | 1 | 4000-00000-00 | Test point / Mounting Hole / Fudicials / Non Component on PCB |  | 1 | ea | J2 | DNP |  | Reference Item | Production | none | none | 1 | 0.0000 |  |  | 0.0000 | 0 | 0 | 0
9 | 1 | 4000-00000-00 | Test point / Mounting Hole / Fudicials / Non Component on PCB |  | 1 | ea | J15 | DNP |  | Reference Item | Production | none | none | 1 | 0.0000 |  |  | 0.0000 | 0 | 0 | 0
10 | 1 | 4004-00010-00 | RES 0402 (1005_m), 1K, 1%, 1/16W, Thick Film |  | 2 | ea | R1,R2 |  |  | Buy | Production | Vishay | CRCW04021K00FKED | 2 | 0.0007 | 0.0014 | Schukat | 0.0000 | 10000 | 10000 | 0
11 | 1 | 4004-00001-00 | RES 0402 (1005_m), 0R (Jumper), 1%, 1/16W, Thick Film |  | 12 | ea | R3,R5,R7,R8,R11,R13,R15,R16,R17,R19,R20,R21 |  |  | Buy | Production | Vishay | CRCW04020000Z0ED | 12 | 0.0003 | 0.0038 | Schukat | 0.0000 | 10000 | 10000 | 0
12 | 1 | 4004-00020-00 | RES 0402 (1005_m), 100R, 1%, 1/16W, Thick Film |  | 4 | ea | R4,R10,R12,R14 |  |  | Buy | Production | Vishay | CRCW0402100RFKED | 4 | 0.0004 | 0.0017 | Schukat | 0.0000 | 10000 | 10000 | 0
13 | 1 | 4004-00100-00 | RES 0402 (1005_m), 30K, 1%, 1/16W, Thick Film |  | 4 | ea | R6,R9,R18,R22 |  |  | Buy | Production | Vishay | CRCW040230K0FKED | 4 | 0.0009 | 0.0038 | ECAS | 0.0000 | 10000 | 10000 | 0
14 | 1 | 4004-02000-00 | RES 0402 (1005_m), 137K, 1%, 1/16W, Thick Film |  | 4 | ea | R23,R24,R25,R26 |  |  | Buy | Production | Vishay | TBA | 4 | 0.0210 | 0.0840 | ECAS | 0.0000 | 1000 | 1000 | 0
15 | 1 | 4000-00000-00 | Test point / Mounting Hole / Fudicials / Non Component on PCB |  | 1 | ea | TP1 | DNP |  | Reference Item | Production | none | none | 1 | 0.0000 |  |  | 0.0000 | 0 | 0 | 0
16 | 1 | 4708-00010-00 | OPA, IC Zero-Drift Op Amp, Rail-to-rail, 2Ch, 8-WSON |  | 2 | ea | U1,U3 |  |  | Buy | Production | TI | TLV2186IDSGR | 2 | 0.4740 | 0.9480 | TI.com | [04/12/23] RFQ to EBV for alternative - NO BID | 3000 | 3000 | 0
17 | 1 | 4706-00030-00 | IC, 3 Phase Meter 40-LFCSP-WQ (6x6) |  | 1 | ea | U2 |  |  | Free Issue | Production | Analog Devices | ADE9430ACPZ | 1 | 7.1900 | 7.1900 |  | [08/09/2023] VT purchased 4,460pcs @ €7.19ea [09/10/2023] Changed from $7.25931 to $6.50 based on 25~30k over 12-2023 thru 01-2025 | 30000 | 2500 | 0
18 | 1 | 4520-00030-00 | ICS, 1.5v~10v Input Switched Capacitor Voltage Converter, -Vin Output, 8-SOIC |  | 1 | ea | U4 |  |  | Buy | Production | TI | LMC7660IMX/NOPB | 1 | 0.4160 | 0.4160 | ECAS | 0.0000 | 1000 | 1 | 0
19 | 1 | 4712-00020-00 | OSC, 24.576MHz XO (Standard) HCMOS, 1v6~3v6 Enable/Disable 4-SMD No Lead |  | 1 | ea | Y2 |  |  | Buy | Production | ECS Inc | ECS-5032MV-245.7-BN-TR | 1 | 0.5133 | 0.5133 | ECAS | [07/12/23] Jauch offer O 24,5760-JO53-3.3-B-1-T1-LF 1k @ $1.04 | 3000 | 3000 | 0
20 | 1 | 4901-30030-05 | PCB, Scavenger ADE (47.5x26x1.6mm, 4L, 1oz/1oz, ENIG, 8-up), ver 4.4 | 24-ECO-012 | 1 | ea | PCB1 |  |  | Buy | Production | EMS Approved | 4901-30030-05 | 1 | 2.4500 | 2.4500 | 0.0000 | 0.0000 | 0 | 0 | 0

Sheet: ECO History
RefDes | VTPN | Parent Rev | Action | ECO | Date | Description | Comment
 |  | 04 | Initial Release |  | 2024-10-09 | #N/A
C2 | 4106-00020-00 | 05 | Remove | 24-ECO-012 | 2024-09-20 | CAP 0603 (1608_m), 100n, 10%, 16V X7R | Changes from ESB FAT Build review
C2 | 4104-00100-00 | 05 | Add | 24-ECO-012 | 2024-09-20 | CAP 0402 (1005_m), 0.1u, 10%, 25V X7R
PCB1 | 4901-30030-04 | 05 | Remove | 24-ECO-012 | 2024-09-20 | PCB, Scavenger ADE (47.5x26x1.6mm, 4L, 1oz/1oz, ENIG, 8-up), ver 4.3
PCB1 | 4901-30030-05 | 05 | Add | 24-ECO-012 | 2024-09-20 | PCB, Scavenger ADE (47.5x26x1.6mm, 4L, 1oz/1oz, ENIG, 8-up), ver 4.4
