acQuire-KL/VT_PCB_PCA/BG95/3902-30029-07/3902-30029-07 - PCA, Scavenger - Communications (GSM), BG95, Ver 4.4 - EUR.xlsx

Sheet: Cost Summary
Batch Size |  | 100
Materials
Components | THT | 1 | 2.6969
Components | SMD | 28 | 12.1998
PCB | PCB |  | 0.8900
Handling | 10% |  | 1.5787
Sub-Total Materials |  |  | 17.3653
Setups
Feeders | 4.50 | 17 | 76.5000
Stencil Control & Clean | 20.00 | 1 | 20.0000
Sub-Total Setup |  |  | 96.5000
Assy Costs
SMT Placement | 0.0135 | 28 | 0.3780
THT Joints | 0.05 | 3 | 0.1500
AOI | 0.0035 | 28 | 0.0980
PCB Seperation | 0.2 | 1 | 0.2000
Batch Cost Amortisation |  |  | 0.9650
Conformal Coating | 1.5 | 1 | 1.5000
Pack & Handling | 0.3 | 1 | 0.3000
Sub-Total Assy |  |  | 3.5910
Batch Size Premium | 25% | 1 | 0.8977
Total Unit Cost |  |  | 21.8541
Markup | 12% |  | 2.6225
Unit Price |  |  | 24.4766
Free Issue
Components | 0 | 0 | 0.0000
WH & Handling | 3% |  | 0.0000
Sub-Total WH & H |  |  | 0.0000
Overheads
SMT Line Pgm | 100 | 1 | 100.0000
AOI Pgm | 100 | 1 | 100.0000
Stencil Vectorguard | 85 | 1 | 85.0000
Sub-Total Overheads |  |  | 285.0000
Grand Total |  |  | 2732.66
Ex Factory Unit |  |  | 27.3266

Sheet: CoO Breakdown
Placement Method | (Multiple Items)
Populate | (blank)
Country Of Origin | Sum of Per Assy. | Value € | Percentage | Percentage of Built Value
China | 7 | 13.3349 | 84.47% | 48.7981803%
Philippines | 3 | 0.0547 | 0.35% | 0.2002445585%
Taiwan | 12 | 0.0154 | 0.10% | 0.05628218769%
United Kingdom | 3 | 0.5250 | 3.33% | 1.921206017%
El Salvador | 2 | 0.8160 | 5.17% | 2.986103066%
France | 2 | 0.7977 | 5.05% | 2.919135313%
Thailand | 1 | 0.2430 | 1.54% | 0.8892439278%
Grand Total | 30 | 15.7867 | 100.00%
Manufacturing, Overheads & Profit (Romania) |  | 11.53990891 |  | 42.22960463%
Ex Factory |  | 27.32658525 |  | 100%

Sheet: BOM
Seq | Level | VTPN | Description | ECO | Qty | UoM | RefDes | Populate | BOM Notes | Type | LifeCycle | MFG | MPN | Per Assy. | Unit € | Value € | Vendor | Parts Master Notes | MOQ | Pack Qty | LT | Country Of Origin | Placement Method | Pin Count | Placement Unit Cost | Placement Value
1 | Parent | 3902-30029-07 | PCA, Scavenger - Communications (GSM), BG95, Ver 4.4 - EUR |  | 1 | ea |  |  |  | Make | Production | ECAS | 0.00 | 1 | 0.0000 | 15.79 |  | 0.0000 | 0 | 0 | 0 | Romania | 0 | 0 | 0.0000 | 0.0000
2 | 1 | 4200-00020-00 | CAP, 3v7 39mAh Hybrid Layer Capacitor, 15x20, 3-pin Solder Tags |  | 1 | ea | BT1 |  |  | Buy | Production | LongSing Technology | HPC-1520 | 1 | 2.6969 | 2.6969 | LongSing Technology Group | 0.0000 | 500 | 500 | 0 | China | THT | 3 | 0.1500 | 0.1500
3 | 1 | 4106-00040-00 | CAP 0603 (1608_m), 33p, 5%, 50V NP0 |  | 3 | ea | C1,C2,C3 |  |  | Buy | Production | Darfon | C1608NP0330JGTS | 3 | 0.0019 | 0.0058 | ECAS | 0.0000 | 4000 | 4000 | 0 | Taiwan | SMD | 0 | 0.0135 | 0.0405
4 | 1 | 4106-00020-00 | CAP 0603 (1608_m), 100n, 10%, 25V X7R |  | 3 | ea | C4,C7,C8 |  |  | Buy | Production | Darfon | C1608X7R104KFTS | 3 | 0.0005 | 0.0015 | Schukat | 0.0000 | 0 | 0 | 0 | Taiwan | SMD | 0 | 0.0135 | 0.0405
5 | 1 | 4128-00100-00 | CAP 2917 (7343_m), 470u, 10%, 6v3 Tant |  | 2 | ea | C5,C6 |  |  | Buy | Production | Kyocera AVX | TAJD477K006RNJ | 2 | 0.4080 | 0.8160 | ECAS | 0.0000 | 0 | 0 | 0 | El Salvador | SMD | 0 | 0.0135 | 0.0270
6 | 1 | 4106-00040-00 | CAP 0603 (1608_m), 33p, 5%, 50V NP0 |  | 2 | ea | C9,C10 | DNP |  | Buy | Production | Darfon | C1608NP0330JGTS | 2 | 0.0019 |  | ECAS | 0.0000 | 4000 | 4000 | 0 |  |  |  |  | 0.0000
7 | 1 | 4106-00010-00 | CAP 0603 (1608_m), 10p, 5%, 50V NP0 |  | 2 | ea | C11,C12 |  |  | Buy | Production | Darfon | C1608NP0100JGTS | 2 | 0.0019 | 0.0038 | ECAS | 0.0000 | 4000 | 4000 | 0 | Taiwan | SMD | 0 | 0.0135 | 0.0270
8 | 1 | 4006-00000-00 | RES 0603 Place Holder |  | 2 | ea | C13,C14 | DNP |  | Reference Item | Production | none | none | 2 | 0.0000 |  |  | 0.0000 | 0 | 0 | 0 |  |  |  |  | 0.0000
9 | 1 | 4724-00010-00 | TVS, 5-Ch, 12.5V Clamp 8A (8/20µs) Ipp, SC-70-6 |  | 1 | ea | D1 |  |  | Buy | Production | Semtech | SMF05C.TCT | 1 | 0.2140 | 0.2140 | ECAS | 0.0000 | 0 | 0 | 0 | China | SMD | 0 | 0.0135 | 0.0135
10 | 1 | 4000-00000-00 | Test point / Mounting Hole / Fudicials / Non Component on PCB |  | 4 | ea | FID1,FID2,FID3,FID4 |  |  | Reference Item | Production | none | none | 4 | 0.0000 |  |  | 0.0000 | 0 | 0 | 0 | None | None | 0 | 0.0000 | 0.0000
11 | 1 | 4000-00000-00 | Test point / Mounting Hole / Fudicials / Non Component on PCB |  | 1 | ea | H1 |  |  | Reference Item | Production | none | none | 1 | 0.0000 |  |  | 0.0000 | 0 | 0 | 0 | None | None | 0 | 0.0000 | 0.0000
12 | 1 | 4402-00020-00 | CON, 2x5-pin, Straight, SMD, B2B Male Header, H=8.00mm, P=2.54mm, 3A |  | 1 | ea | J2 |  |  | Buy | Production | Amphenol FCI | 95278-102B10LF | 1 | 0.3668 | 0.3668 | ECAS | 0.0000 | 5000 | 0 | 0 | France | SMD | 0 | 0.0135 | 0.0135
13 | 1 | 4402-00030-00 | CON, 2x8-pin, Straight, SMD, B2B Male Header, H=8.00mm, P=2.54mm, 3A |  | 1 | ea | J3 |  |  | Buy | Production | Amphenol FCI | 95278-102B16LF | 1 | 0.4309 | 0.4309 | ECAS | 0.0000 | 1 | 0 | 0 | France | SMD | 0 | 0.0135 | 0.0135
14 | 1 | 4753-00010-00 | HDW, Cable Clamp, SMD, 5x5x2mm, Ø1.0 ~ 1.5mm |  | 3 | ea | J4,J5,J6 |  |  | Buy | Production | Harwin | S8111-46R | 3 | 0.1750 | 0.5250 | ECAS | 0.0000 | 0 | 0 | 0 | United Kingdom | SMD | 0 | 0.0135 | 0.0405
15 | 1 | 4414-00020-00 | CON, 6-Pos MicroSIM Cage, Push-Pull, No Detect, H=1.45mm, SMD |  | 1 | ea | J11 |  | • Fit "Test SIM" before starting initial Test • Replace with "Final SIM" after passing Test | Buy | Production | Molex | 78646-3001 | 1 | 0.7900 | 0.7900 | ECAS | RFQ before next build | 57 | 1 | 0 | China | SMD | 0 | 0.0135 | 0.0135
16 | 1 | 4416-00010-00 | CON, U.FL (UMCC) Jack, Male Pin 50Ohm SMD |  | 1 | ea | J12 |  |  | Buy | Production | TE Connectivity | 2337019-1 | 1 | 0.0061 | 0.0061 | ECAS | 0.0000 | 55 | 1 | 0 | China | SMD | 0 | 0.0135 | 0.0135
17 | 1 | 4500-00020-00 | TRN, BJT NPN - Pre-Biased R1=4K7 R2=0R, Vce=50V 100mA 200mW, SMD, TO-236-3, SC-59, SOT-23-3 |  | 3 | ea | Q1,Q3,Q8 |  |  | Buy | Production | Rohm | DTC143TKAT146 | 3 | 0.0182 | 0.0547 | ECAS | Confirm Package | 3000 | 0 | 0 | Philippines | SMD | 0 | 0.0135 | 0.0405
18 | 1 | 4530-00010-00 | FET, P-Channel 30 V 6.5A (Ta) 3.1W (Ta), 8-SOP |  | 1 | ea | Q2 |  |  | Buy | Production | UMW | AO4459 | 1 | 0.0630 | 0.0630 | ECAS | 0.0000 | 500 | 1 | 0 | China | SMD | 0 | 0.0135 | 0.0135
19 | 1 | 4006-00160-00 | RES 0603 (1608_m), 15K, 1%, 1/10W, Thick Film |  | 1 | ea | R1 |  |  | Buy | Production | Vishay | CRCW060315K0FKEA | 1 | 0.0010 | 0.0010 | Schukat | 0.0000 | 5000 | 5000 | 0 | Taiwan | SMD | 0 | 0.0135 | 0.0135
20 | 1 | 4006-00150-00 | RES 0603 (1608_m), 4K7, 1%, 1/10W, Thick Film |  | 2 | ea | R2,R3 |  |  | Buy | Production | Vishay | CRCW06034K70FKEA | 2 | 0.0012 | 0.0023 | Schukat | 0.0000 | 5000 | 5000 | 0 | Taiwan | SMD | 0 | 0.0135 | 0.0270
21 | 1 | 4006-00001-00 | RES 0603 (1608_m), 0R (Jumper), 1%, 1/10W, Thick Film |  | 1 | ea | R4 |  |  | Buy | Production | Vishay Dale | CRCW06030000Z0EA | 1 | 0.0009 | 0.0009 | Schukat | 0.0000 | 5000 | 5000 | 0 | Taiwan | SMD | 0 | 0.0135 | 0.0135
22 | 1 | 4000-00000-00 | Test point / Mounting Hole / Fudicials / Non Component on PCB |  | 1 | ea | TP1 |  |  | Reference Item | Production | none | none | 1 | 0.0000 |  |  | 0.0000 | 0 | 0 | 0 | None | None | 0 | 0.0000 | 0.0000
23 | 1 | 4716-00010-00 | MDM, Cellular, GSM, LTE Transceiver Module 850MHz, 900MHz, 1.8GHz, 1.9GHz, SMD Module, No Antenna |  | 1 | ea | U1 |  |  | Buy | Production | Quectel | BG95M3LA-64-SGNS | 1 | 8.6749 | 8.6749 | FMG Electronics | [21/11/23] FMG revised quote from 1k @ $11.29 to 4k @ $9.80 with 1k schedule; allow 250pcs shipments. [22/11/23] FMG revised 4k $9.80 to $9.65 [28/11/23] FMG offer 1k @ $9.80 [12/12/23] FMG to keep 1k EAU @ $9.65 (4x 250pcs drops) | 1000 | 250 | 0 | China | SMD | 0 | 0.0135 | 0.0135
24 | 1 | 4702-00010-00 | IC, 4-Bit Bi-Directional Tri-State Level Shifter, Auto Detect Direction, 12-UQFN |  | 1 | ea | U2 |  |  | Buy | Production | TI | TXB0104RUT | 1 | 0.2430 | 0.2430 | ECAS | 0.0000 | 100 | 1 | 0 | Thailand | SMD | 0 | 0.0135 | 0.0135
25 | 1 | 4902-30029-06 | PCB, Scavenger GSM, BG95 (71.00x25.50mm, 4-L, Cu, ENIG), ver 4.4 |  | 1 | ea | PCB1 |  |  | Buy | Production | EMS Approved | 4902-30029-06 | 1 | 0.8900 | 0.8900 | ECAS | 0.0000 | 200 | 200 | 0 | China | PCB | 0 | 0.0000 | 0.0000

Sheet: ECO History
RefDes | VTPN | Parent Rev | Action | ECO | Date | Description | Comment
 |  | 04 | Initial Release |  | 2024-04-18 | #N/A
 |  | 05 |  |  |  | #N/A
 |  | 06 |  |  | 2024-04-18 | #N/A
 |  | 07 |  |  | 2024-10-31 | #N/A
 |  |  |  |  |  | #N/A
 |  |  |  |  |  | #N/A
