acQuire-KL/VT_PCB_PCA/ADE/3901-30030-04/3901-30030-04 - PCA, Scavenger - ADE Channel (ADE) ver 4.3.xlsx

Sheet: Scavenger BOM
Seq | Level | VTPN | Description | ECO | Qty | UoM | RefDes | BOM Notes | Type | LifeCycle | MFG | MPN | Per Assy. | Unit € | Value € | Vendor | Parts Master Notes | MOQ | Pack Qty | LT
1 | Parent | 3901-30030-04 | PCA, Scavenger - ADE Channel (ADE), ver 4.3 | 24-ECO-001 | 1 | EA |  |  | Make | UnReleased | ECAS + Delta | 3901-30030-04 | 1 | 0.0000 | 0.00348 |  | 0.0000 | 0 | 0 | 0
2 | 1 | 4004-02000-00 | RES 0402 (1005_m), 137K, 1%, 1/16W, Thick Film |  | 4 | EA | R25,R26,R24,R23 |  | Buy | Production | Yageo | RC0402FR-07137KL | 4 | 0.0009 | 0.0035 | ECAS | 0.0000 | 10000 | 0 | 18
3 | 1 | 4004-00100-00 | RES 0402 (1005_m), 30K, 1%, 1/16W, Thick Film |  | 4 |  | R18,R9,R6,R22 |  | Buy | Production | Yageo | RC0402FR-0730KL | 4 | 0.0009 | 0.0035 | ECAS | 0.0000 | 10000 | 0 | 18
4 | 1 | 4004-00001-00 | RES 0402 (1005_m), 0R (Jumper), 1%, 1/16W, Thick Film |  | 12 |  | R5,R20,R8,R11,R15,R21,R17,R7,R16,R3,R19,R13 |  | Buy | Production | Bourns Inc | CR0402AJ/-000GLF | 12 | 0.0009 | 0.0104 | ECAS | 0.0000 | 10000 | 10000 | 15
5 | 1 | 4104-00020-00 | CAP 0402 (1005_m), 22n, 5%, 25V X7R |  | 5 |  | C11,C3,C7,C1,C9 |  | Buy | Production | Kemet | C0402C223J3RAC7867 | 5 | 0.0320 | 0.1600 | ECAS | 0.0000 | 10000 | 10000 | 27
6 | 1 | 4104-00100-00 | CAP 0402 (1005_m), 0.1u, 10%, 25V X7R |  | 14 |  | C13,C15,C16,C17,C6,C5,C21,C29,C23,C14,C30,C19,C28,C27 |  | Buy | Production | Murata | GRM155R71E104KE14D | 14 | 0.0030 | 0.0420 | ECAS | 0.0000 | 5000 | 5000 | 19
7 | 1 | 4112-00100-00 | CAP 1206 (3216_m), 10u, 10%, 25V X7R |  | 6 |  | C26,C18,C25,C20,C22,C24 |  | Buy | Production | Samsung | CL31B106KAHNFNE | 6 | 0.0254 | 0.1523 | ECAS | 0.0000 | 2000 | 0 | 22
8 | 1 | 4106-00020-00 | CAP 0603 (1608_m), 100n, 5%, 25V X7R |  | 1 |  | C2 |  | Buy | Production | Yageo | CC0603JRX7R8BB104 | 1 | 0.0043 | 0.0043 | ECAS | 0.0000 | 4000 | 0 | 16
9 | 1 | 4004-00010-00 | RES 0402 (1005_m), 1K, 1%, 1/16W, Thick Film |  | 2 |  | R1,R2 |  | Buy | Production | Yageo | RC0402FR-071KP | 2 | 0.0009 | 0.0017 | ECAS | 0.0000 | 10000 | 10000 | 18
10 | 1 | 4104-00000-00 | CAP 0402, Place Holder, No Value, Not Fitted |  | 4 |  | C4,C12,C10,C8 |  | Reference Item | Production | VT Electron | None | 4 | 0.0000 |  |  | 0.0000 | 0 | 0 | 0
11 | 1 | 4004-00020-00 | RES 0402 (1005_m), 100R, 1%, 1/16W, Thick Film |  | 4 |  | R4,R14,R10,R12 |  | Buy | Production | Stackpole | RMCF0402FT100R | 4 | 0.0009 | 0.0035 | ECAS | 0.0000 | 10000 | 0 | 16
12 | 1 | 4708-00010-00 | OPA, IC Zero-Drift Op Amp, Rail-to-rail, 2Ch, 8-WSON |  | 2 |  | U3,U1 |  | Buy | Production | TI | TLV2186IDSGR | 2 | 0.4740 | 0.9480 | TI.com | [04/12/23] RFQ to EBV for alternative - NO BID | 3000 | 3000 | 6
13 | 1 | 4706-00030-00 | IC, 3 Phase Meter 40-LFCSP-WQ (6x6) |  | 1 |  | U2 |  | Free Issue | Production | Analog Devices | ADE9430ACPZ-RL | 1 | 7.1900 | 7.1900 |  | [08/09/2023] VT purchased 4,460pcs @ €7.19ea [09/10/2023] Changed from $7.25931 to $6.50 based on 25~30k over 12-2023 thru 01-2025 | 30000 | 2500 | 13
14 | 1 | 4712-00020-00 | OSC, 24.576MHz XO (Standard) HCMOS, 1v6~3v6 Enable/Disable 4-SMD No Lead |  | 1 |  | Y2 |  | Buy | Production | ECS Inc | ECS-5032MV-245.7-BN-TR | 1 | 0.5133 | 0.5133 | ECAS | [07/12/23] Jauch offer O 24,5760-JO53-3.3-B-1-T1-LF 1k @ $1.04 | 3000 | 3000 | 13
15 | 1 | 4408-00010-00 | CON, 1x8-Pin, M, R/A, SMD, W2B, 4-Shroud, 2.50mm, 3A 250V |  | 1 |  | J1 |  | Buy | Production | Zhejiang Lianhe Electronics Co Ltd | A2501-SR08-XH8AWB | 1 | 0.0000 | 0.0000 | ECO Cables | [12/09/2023] Zhejiang Lianhe offer 1k @ $0.0389, 10k @ €0.0354 [12/12/2023] Supplied with M12 Pre-Wired Assembly by Eco Cables China | 1000 | 1000 | 3
16 | 1 | 4401-00030-00 | CON, 1x8-pin, Straight, THP, B2B Male Header, P=2.54mm, 3A |  | 0 |  | J15 | DNP | Buy | Production | Connfly | DS1021-1*8SF11-B | 0 | 0.0408 | 0.0000 | TME | 0.0000 | 1000 | 1000 | 31
17 | 1 | 4520-00030-00 | ICS, 1.5v~10v Input Switched Capacitor Voltage Converter, -Vin Output, 8-SOIC |  | 1 |  | U4 |  | Buy | Production | TI | LMC7660IMX/NOPB | 1 | 0.5658 | 0.5658 | TI.com | 0.0000 | 1000 | 1 | 12
18 | 1 | 4901-30030-04 | PCB, Scavenger ADE (47.5x26x1.6mm, 4L, 1oz/1oz, ENIG, 8-up), ver 4.3 |  | 1 |  | PCB1 |  | Buy | Production | EMS Approved | 4901-30030-04 | 1 | 2.4500 | 2.4500 | ECAS | 0.0000 | 0 | 0 | 0

Sheet: ADE_Main_V4
Id | Designator | Package | Quantity | Designation | Supplier and ref | Column1 | _1
1 | R25,R26,R24,R23 | R_0402_1005Metric | 4 | 137K | 4004-02000-00
2 | R18,R9,R6,R22 | R_0402_1005Metric | 4 | 30K | 4004-00100-00
3 | R5,R20,R8,R11,R15,R21,R17,R7,R16,R3,R19,R13 | R_0402_1005Metric | 12 | 0 | 4004-00001-00
4 | C11,C3,C7,C1,C9 | C_0402_1005Metric | 5 | 22n | 4104-00020-00
5 | C13,C15,C16,C17,C6,C5,C21,C29,C23,C14,C30,C19,C28,C27 | C_0402_1005Metric | 14 | 100n | 4104-00100-00
6 | FID1,FID4,FID3,FID2 | Fiducial_1mm_Mask2mm | 4 | Fiducial | Non Component
7 | C26,C18,C25,C20,C22,C24 | C_1206_3216Metric | 6 | 10u | 4112-00100-00
8 | C2 | C_0603_1608Metric | 1 | 100n | 4106-00020-00
9 | R1,R2 | R_0402_1005Metric | 2 | 1k | 4004-00010-00
10 | C4,C12,C10,C8 | C_0402_1005Metric | 4 | DNP | 4104-00000-00
11 | R4,R14,R10,R12 | R_0402_1005Metric | 4 | 100 | 4004-00020-00
12 | U3,U1 | WSON-8-1EP_2x2mm_P0.5mm_EP0.9x1.6mm_ThermalVias | 2 | TLV2186IDSGR | 4708-00010-00
13 | TP1 | Eticheta | 1 | Eticheta | Non Component
14 | U2 | ADE9430 | 1 | ADE9430 | 4706-00030-00
15 | Y2 | OSC_ECS-5032MV-245.7-BN-TR | 1 | ECS-5032MV-245.7-BN-TR | 4712-00020-00
16 | J1 | A2501-SR08-XH8AWB | 1 | MUAS100-8-C-E | 4408-00010-00
17 | J15 | PinHeader_1x08_P2.54mm_Vertical | 1 | MUAS100-8-C-E | 4401-00030-00
18 | J2 | BUS_PCIexpress_x1 | 1 | Bus_PCI_Express_x1_MOD | Non Component
19 | U4 | SO-8_3.9x4.9mm_P1.27mm | 1 | MC7660DR2 | 4520-00030-00
