acQuire-KL/VT_PCB_PCA/_From_Cornel/Scavenger - V4.4 Cornel 24-10-31/BG95_Version4_4L/MFG_PACK 3902-30029-07/3902-30029-07_Stack -- Comms BG95 v4.4.xlsx

ID | Type | Color | Material | Thickness (mm) | EpsilonR | LossTg
F.Silkscreen | Top Silk Screen | White
F.Paste | Top Solder Paste
F.Mask | Top Solder Mask | Green |  | 0.010 | 3.300 | 0.000
F.Cu | copper |  |  | 0.035
Dielectric 1 | core |  | FR4 | 0.480 | 4.500 | 0.020
In1.Cu | copper |  |  | 0.035
Dielectric 2 | prepreg |  | FR4 | 0.480 | 4.500 | 0.020
In2.Cu | copper |  |  | 0.035
Dielectric 3 | core |  | FR4 | 0.480 | 4.500 | 0.020
B.Cu | copper |  |  | 0.035
B.Mask | Bottom Solder Mask | Green |  | 0.010 | 3.300 | 3.300
B.Paste | Bottom Solder Paste
B.Silkscreen | Bottom Silk Screen | White
 |  |  | Board Thickness: | 1.600
