acQuire-KL/VT_PCB_PCA/_From_Cornel/H2Scan_Main_V5_4-pin - Cornel 20-09-2024/MFG_PACK - 3907-00010-01/SCH_3907-00010-01 -- Main H2 (Main), 4-pin, V5.0.pdf

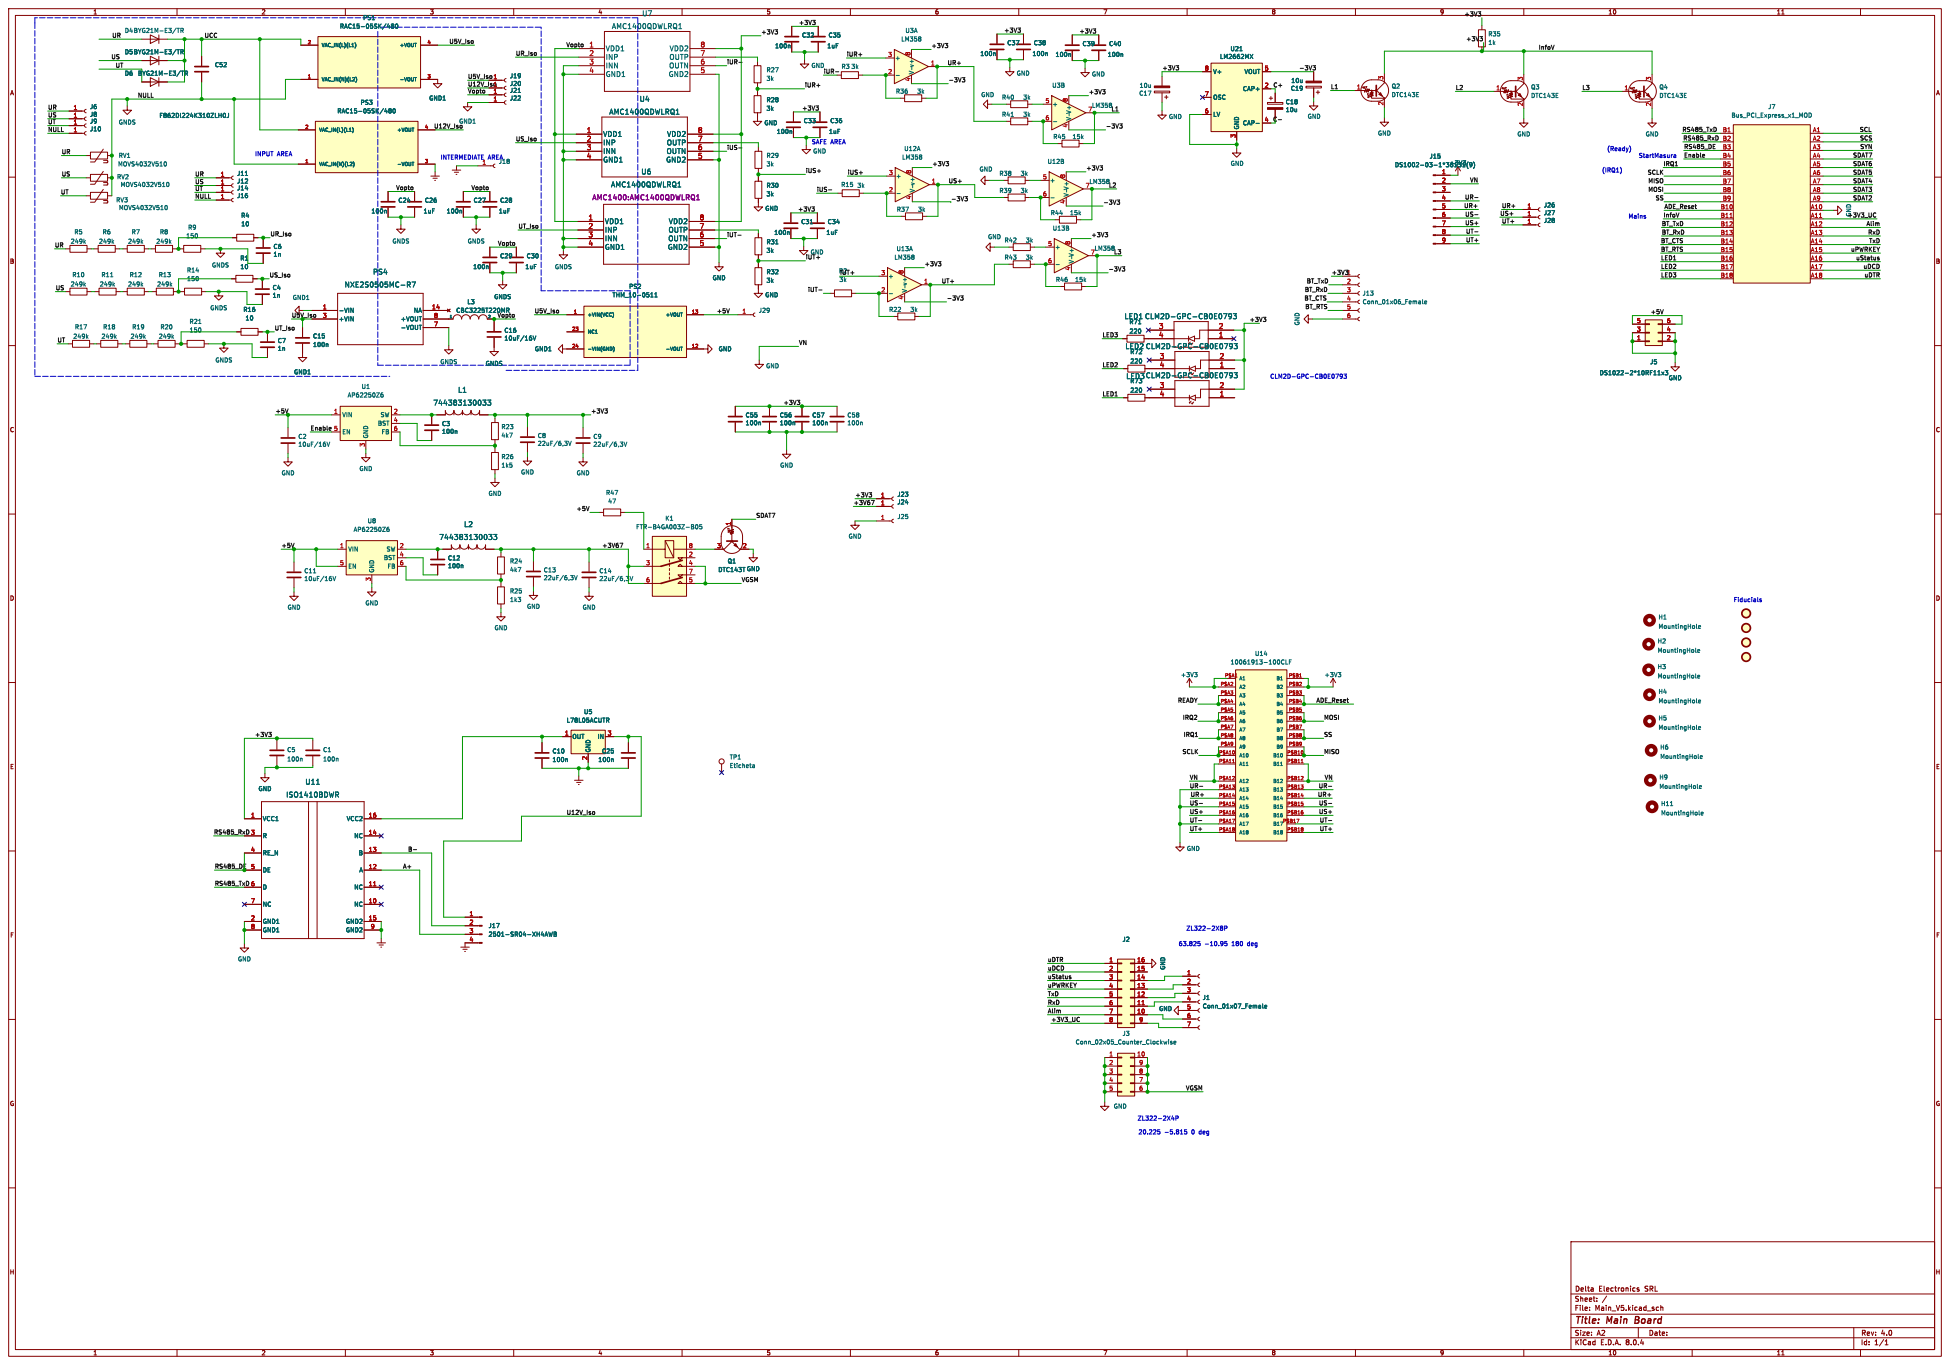
[picture p22: page 1]

3 BST 4 EN 5 FB 6 U8 AP62250Z6 TP1 Eticheta OUT 1 GND
