acQuire-KL/VT_PCB_PCA/_From_Cornel/Scavenger - V4.4 Cornel 24-08-31/Scavenger- V4.4/BG95_Version4_4L/BG95V4.kicad_pcb

## KiCad design _From_Cornel/Scavenger - V4.4 Cornel 24-08-31/Scavenger- V4.4/BG95_Version4_4L/BG95V4.kicad_pcb (2025-04-03)

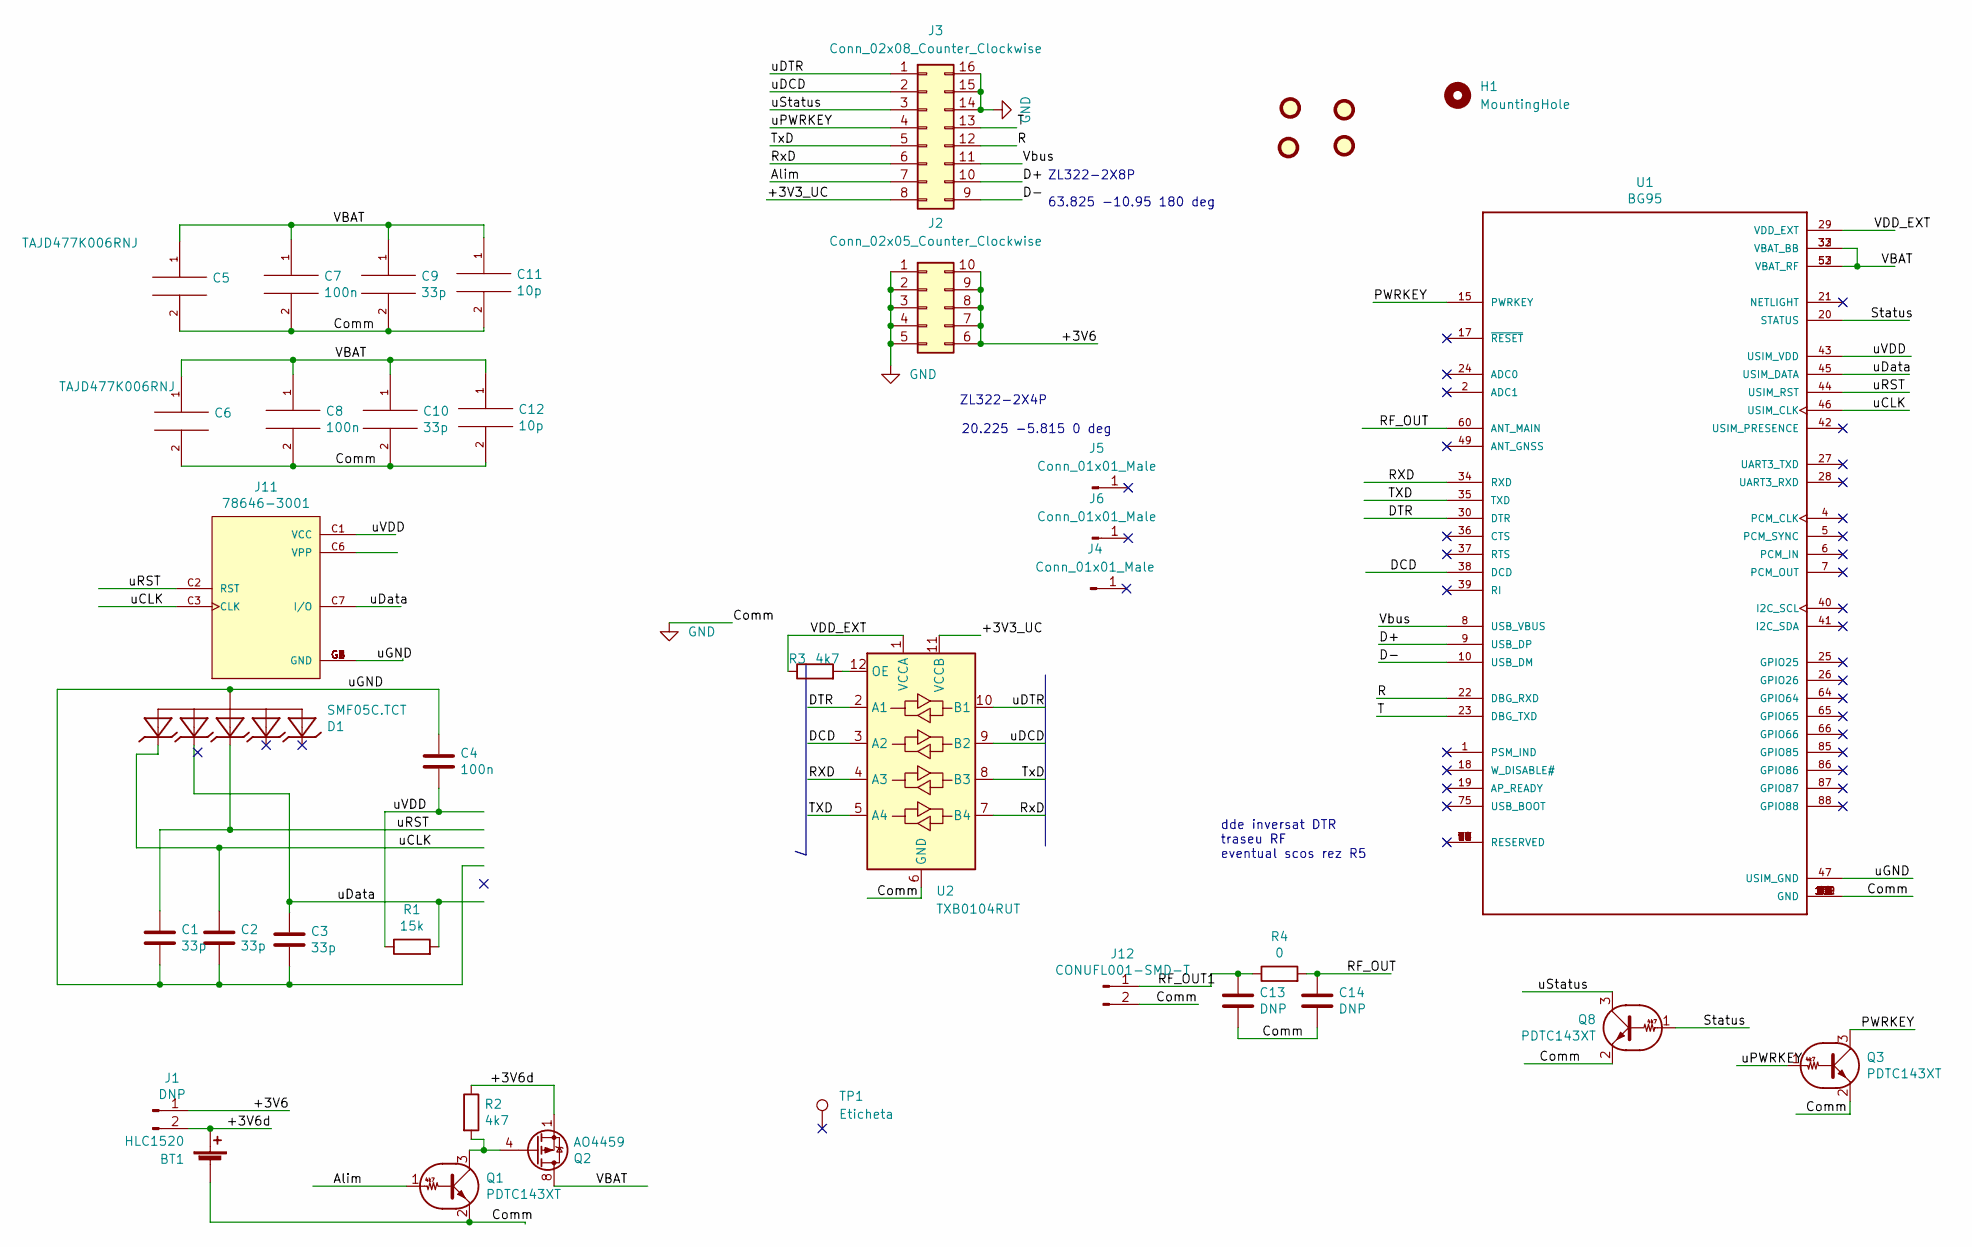
[picture p38: schematic BG95V4.kicad_sch, Modem BG95]

Parts:
BT1: HLC1520
C1, C2, C3: 33p; C_0603_1608Metric
C4: 100n; C_0603_1608Metric
C5, C6: TAJD477K006RNJ; CP_EIA-7361-38_AVX-V_Pad2.18x3.30mm_HandSolder
C7, C8: 100n; C_0603_1608Metric_Pad1.05x0.95mm_HandSolder
C9, C10: 33p; C_0603_1608Metric_Pad1.05x0.95mm_HandSolder
C11, C12: 10p; C_0603_1608Metric_Pad1.05x0.95mm_HandSolder
C13, C14: DNP; C_0603_1608Metric
D1: SMF05C.TCT; SC70-6
FID1, FID2, FID3, FID4: Fiducial; Fiducial_1mm_Mask2mm
H1: MountingHole; MountingHole_2.5mm Simpla
J1: DNP; PinHeader_1x02_P2.54mm_Vertical
J2: Conn_02x05_Counter_Clockwise; PinHeader_2x05_P2.54mm_Vertical_SMD_MOD
J3: Conn_02x08_Counter_Clockwise; PinHeader_2x08_P2.54mm_Vertical_SMD_MOD
J4, J5, J6: Conn_01x01_Male; TestPoint_Pad_5.1x5.1mm
J11: 78646-3001; MOLEX_78646-3001; DIGI-KEY_PART_NUMBER WM9364CT-ND
J12: CONUFL001-SMD-T; U.FL_Molex_MCRF_73412-0110_Vertical
Q1, Q3, Q8: PDTC143XT; SOT-23
Q2: AO4459; SOIC-8_3.9x4.9mm_P1.27mm
R1: 15k; R_0603_1608Metric
R2, R3: 4k7; R_0603_1608Metric
R4: 0; R_0603_1608Metric
TP1: Eticheta
U1: BG95; XCVR_BG95M3LA-64-SGNS
U2: TXB0104RUT; Texas_R_PUQFN-N12

Connections:
/+3V3_UC: J3.8, U2.11 (VCCB)
/+3V6: J1.1, J2.6, J2.7, J2.8, J2.9, J2.10
/+3V6d: BT1.1 (+), J1.2, Q2.1 (S), Q2.2 (S), Q2.3 (S), R2.1
/Alim: J3.7, Q1.1 (B)
/D+: J3.10, U1.9 (USB_DP)
/D-: J3.9, U1.10 (USB_DM)
/DCD: U1.38 (DCD), U2.3 (A2)
/DTR: U1.30 (DTR), U2.2 (A1)
/PWRKEY: Q3.3 (C), U1.15 (PWRKEY)
/R: J3.12, U1.22 (DBG_RXD)
/RF_OUT: C14.1, R4.2, U1.60 (ANT_MAIN)
/RF_OUT1: C13.1, J12.1, R4.1
/RXD: U1.34 (RXD), U2.4 (A3)
/RxD: J3.6, U2.7 (B4)
/Status: Q8.1 (B), U1.20 (STATUS)
/T: J3.13, U1.23 (DBG_TXD)
/TXD: U1.35 (TXD), U2.5 (A4)
/TxD: J3.5, U2.8 (B3)
/VBAT: C5.1, C6.1, C7.1, C8.1, C9.1, C10.1, C11.1, C12.1, Q2.5 (D), Q2.6 (D), Q2.7 (D), Q2.8 (D), U1.32 (VBAT_BB), U1.33 (VBAT_BB), U1.52 (VBAT_RF), U1.53 (VBAT_RF)
/VDD_EXT: R3.1, U1.29 (VDD_EXT), U2.1 (VCCA)
/Vbus: J3.11, U1.8 (USB_VBUS)
/uCLK: C2.1, D1.6, J11.C3 (CLK), U1.46 (USIM_CLK)
/uDCD: J3.2, U2.9 (B2)
/uDTR: J3.1, U2.10 (B1)
/uData: C3.1, D1.5, J11.C7 (I/O), R1.2, U1.45 (USIM_DATA)
/uGND: C1.2, C2.2, C3.2, C4.1, D1.2, J11.C5 (GND), J11.G1 (GND), J11.G2 (GND), J11.G3 (GND), J11.G4 (GND), J11.G5 (GND), J11.G6 (GND), U1.47 (USIM_GND)
/uPWRKEY: J3.4, Q3.1 (B)
/uRST: C1.1, D1.4, J11.C2 (RST), U1.44 (USIM_RST)
/uStatus: J3.3, Q8.3 (C)
/uVDD: C4.2, J11.C1 (VCC), R1.1, U1.43 (USIM_VDD)
GND: BT1.2 (-), C5.2, C6.2, C7.2, C8.2, C9.2, C10.2, C11.2, C12.2, C13.2, C14.2, J2.1, J2.2, J2.3, J2.4, J2.5, J3.14, J3.15, J3.16, J12.2, Q1.2 (E), Q3.2 (E), Q8.2 (E), U1.3 (GND), U1.31 (GND), U1.48 (GND), U1.50 (GND), U1.54 (GND), U1.55 (GND), U1.58 (GND), U1.59 (GND), U1.61 (GND), U1.62 (GND), U1.67 (GND), U1.68 (GND), U1.69 (GND), U1.70 (GND), U1.71 (GND), U1.72 (GND), U1.73 (GND), U1.74 (GND), U1.79 (GND), U1.80 (GND), U1.81 (GND), U1.82 (GND), U1.89 (GND), U1.90 (GND), U1.91 (GND), U1.100 (GND), U1.101 (GND), U1.102 (GND), U2.6 (GND)
unnamed: Q1.3 (C), Q2.4 (G), R2.2
unnamed: R3.2, U2.12 (OE)

Notes on the sheet:
ZL322-2X8P
20.225 -5.815 0 deg
dde inversat DTR traseu RF eventual scos rez R5
ZL322-2X4P
63.825 -10.95 180 deg

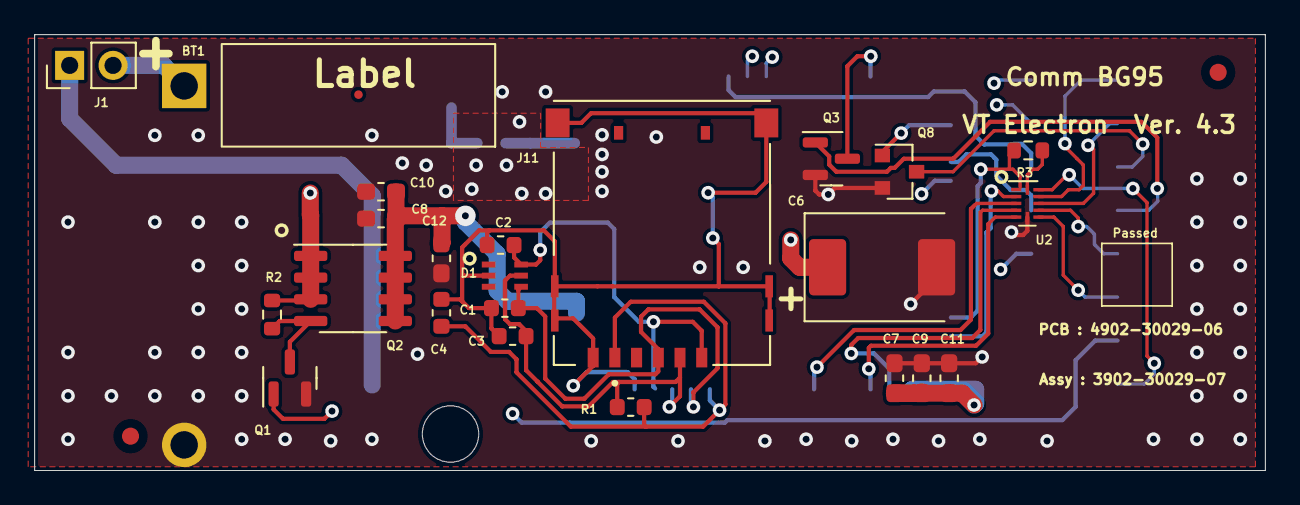
[picture p39: board BG95V4.kicad_pcb from above]

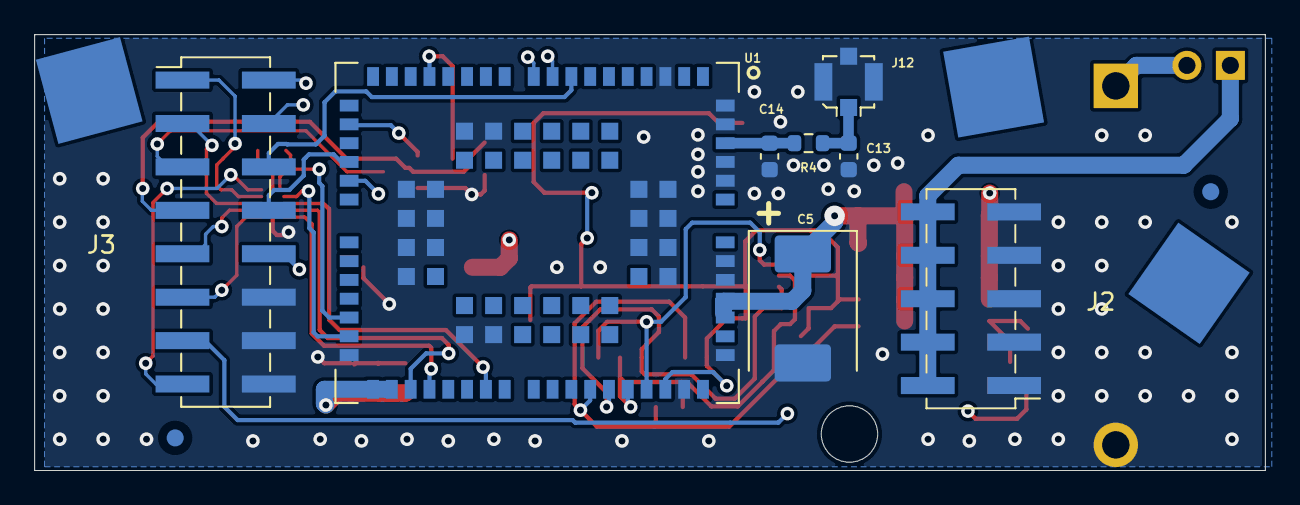
[picture p40: board BG95V4.kicad_pcb from below]

Board: 4 copper layers, 72.0 x 25.5 mm, 40 parts (13 on the bottom side), 33 nets.
